blueintegral/Level/firmware/SimpliciTI-CCS-1.1.1/Components/bsp/boards/CC430EM/schematics/EM430F6137RF900.pdf

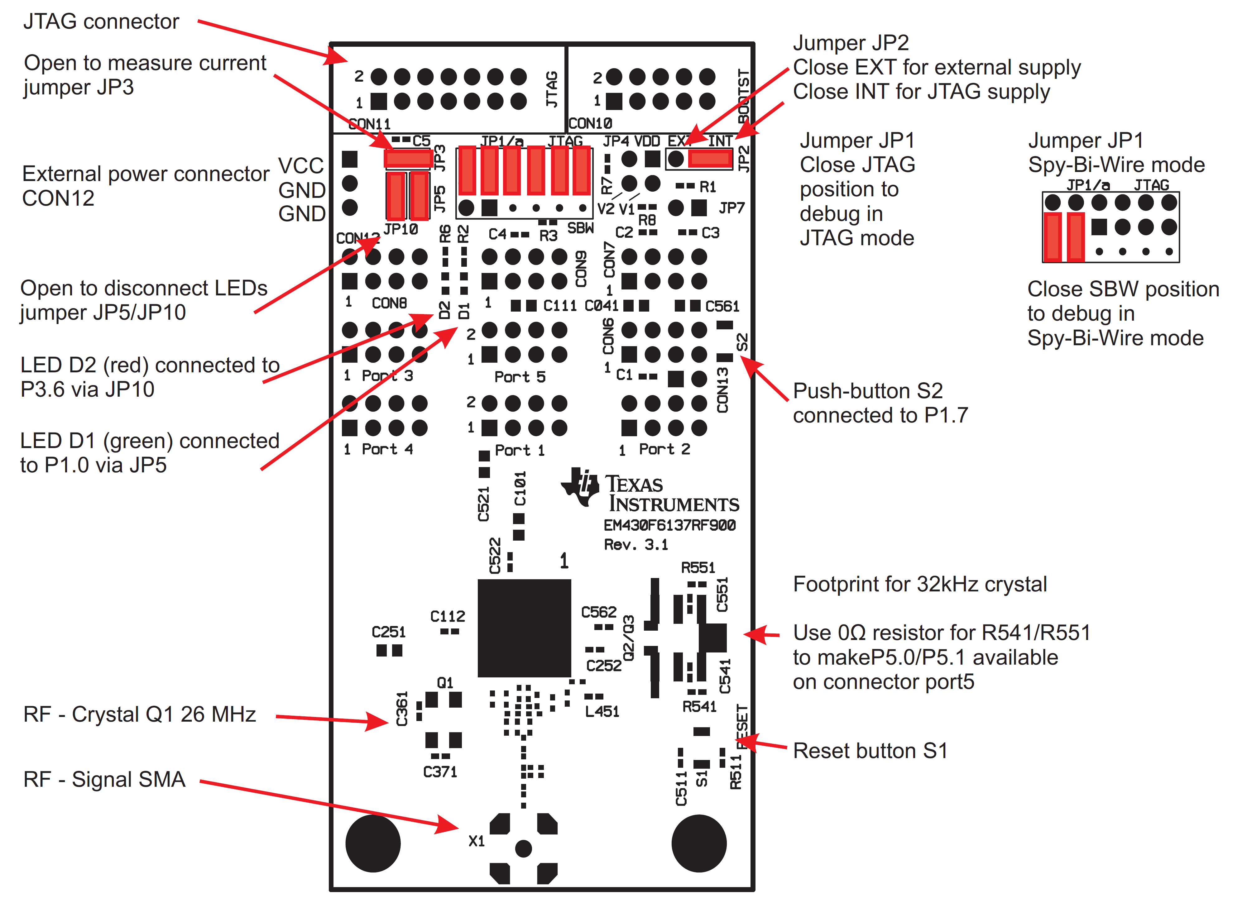
[picture p4: page 1]
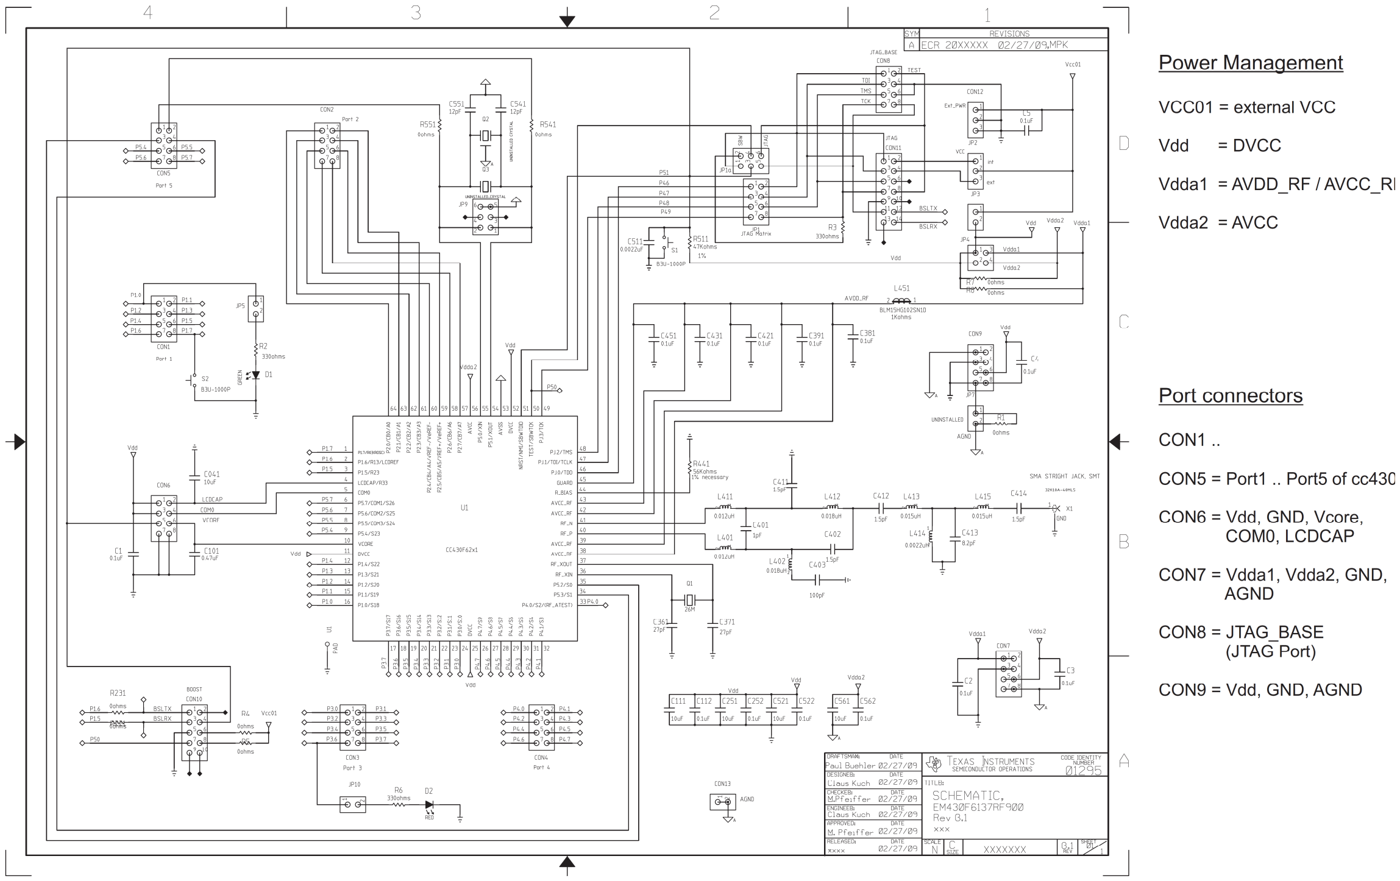
[picture p5: page 2]
