blueintegral/Level/firmware/SimpliciTI-CCS-1.1.1/Components/bsp/boards/EXP461x/schematics/MSP-EXP430FG4618 Schematic.pdf

RF Daughter Card Connect | Isolated RS232 Communication
MSP430FG4618 Pin Access | Power Supply Configuration

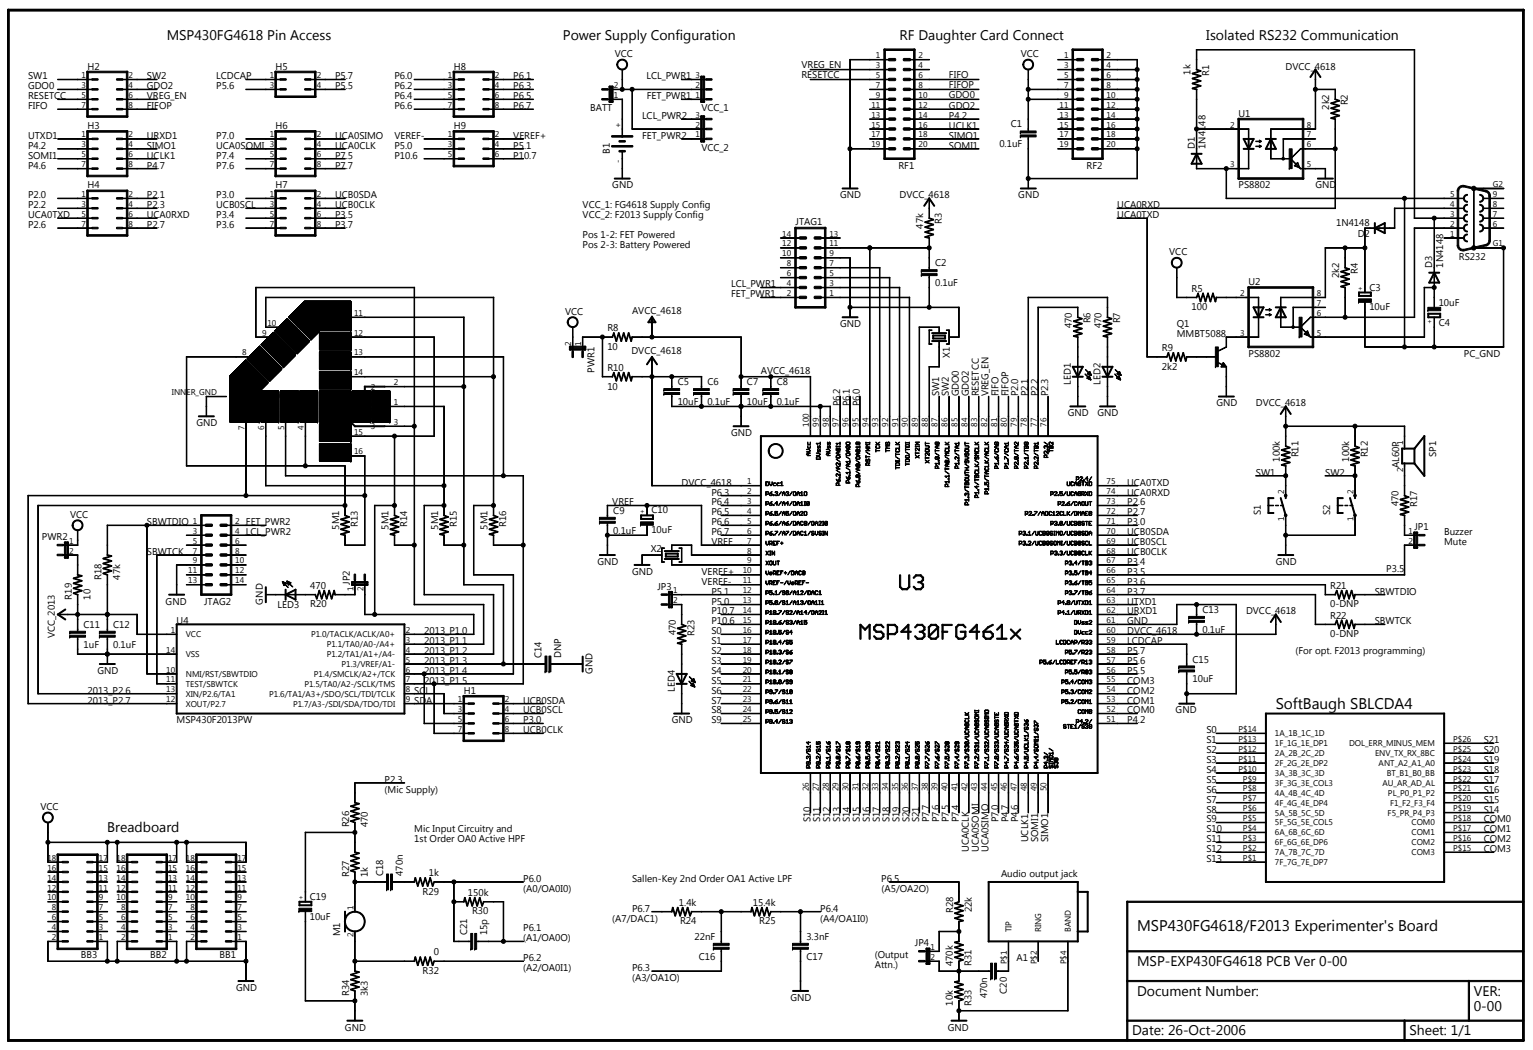
[picture p22: page 1]

P1.6/TA1/A3+/SDO/SCL/TDI/TCLK 8

Mic Input Circuitry and
1st Order OA0 Active HPF

Sallen-Key 2nd Order OA1 Active LPF
