blueintegral/Level/hardware/Tag Connect footprints/Altium/tc2050-b/totc/tc2050example.pdf

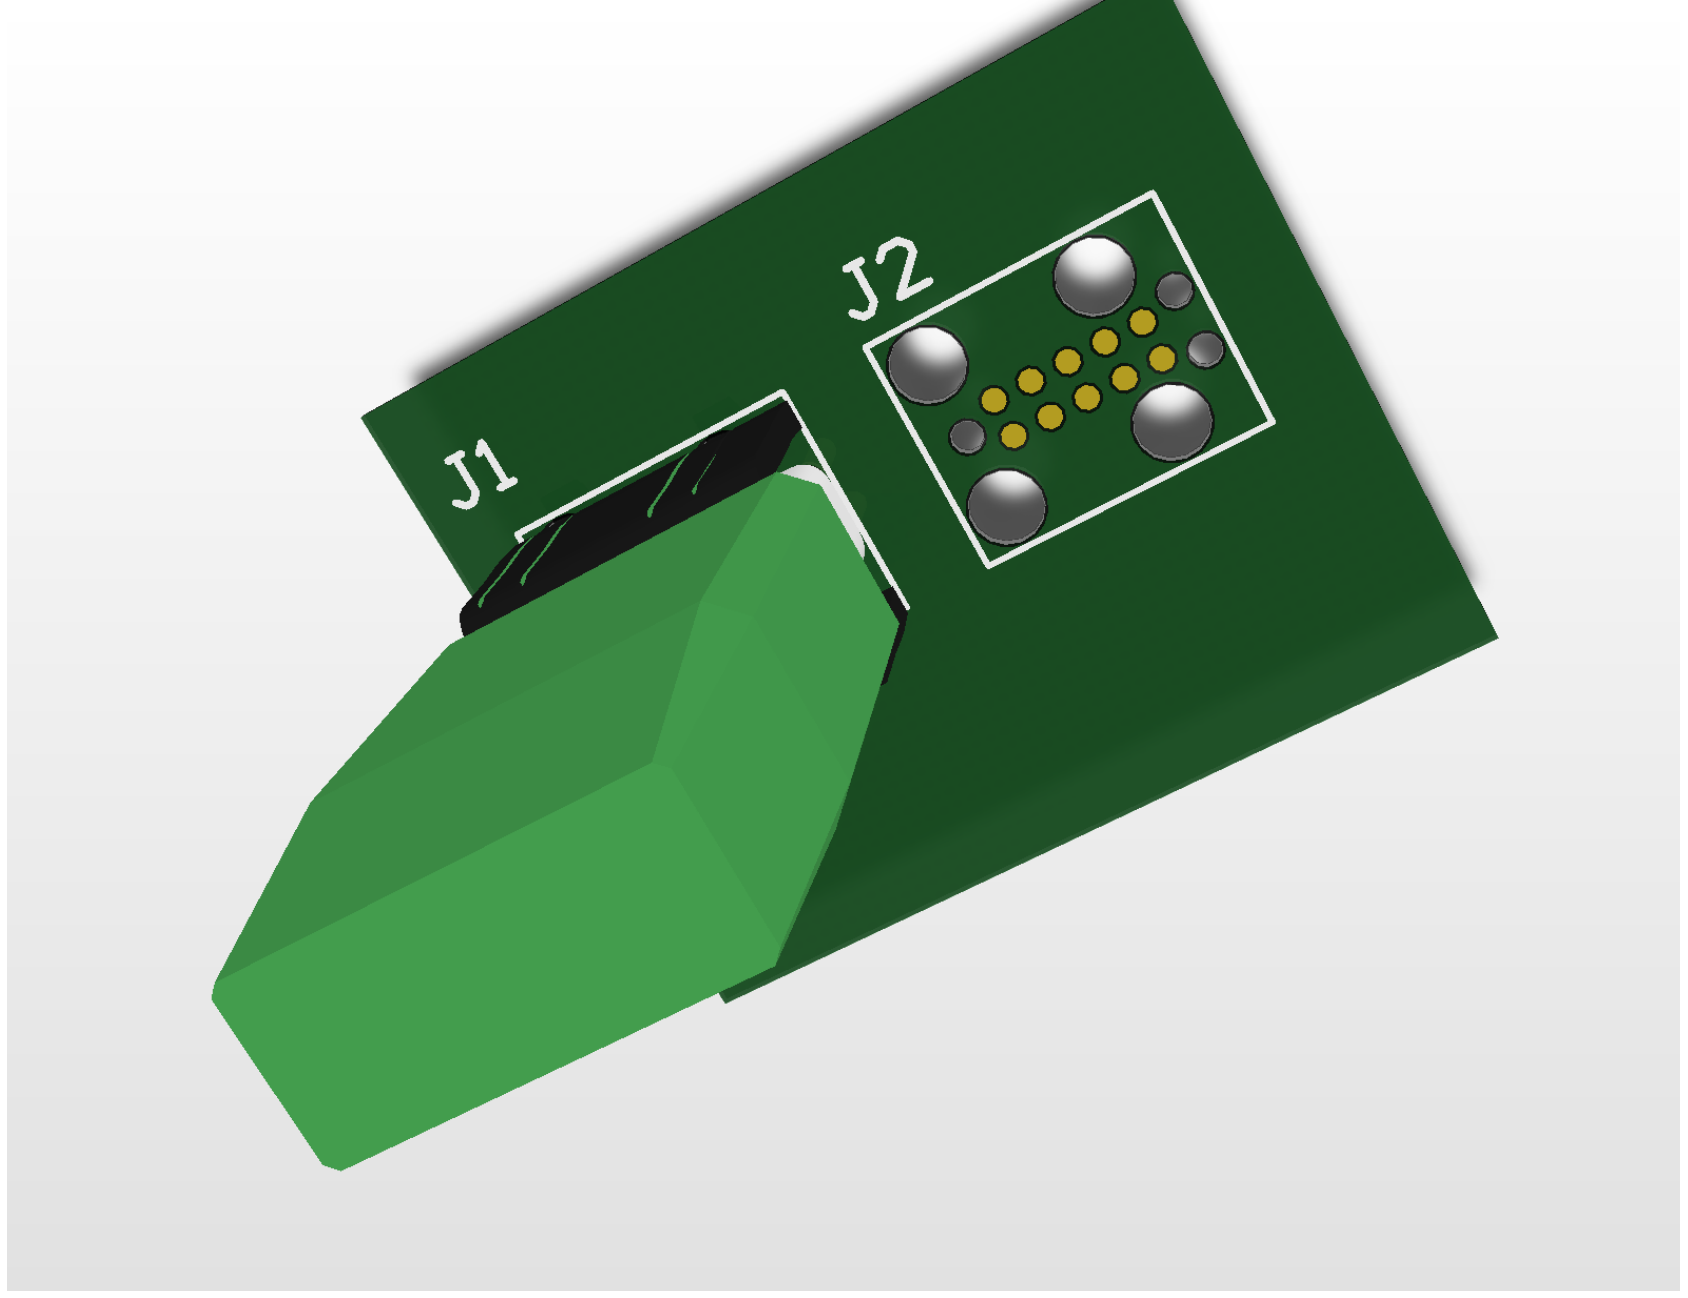
[picture p27: page 1]

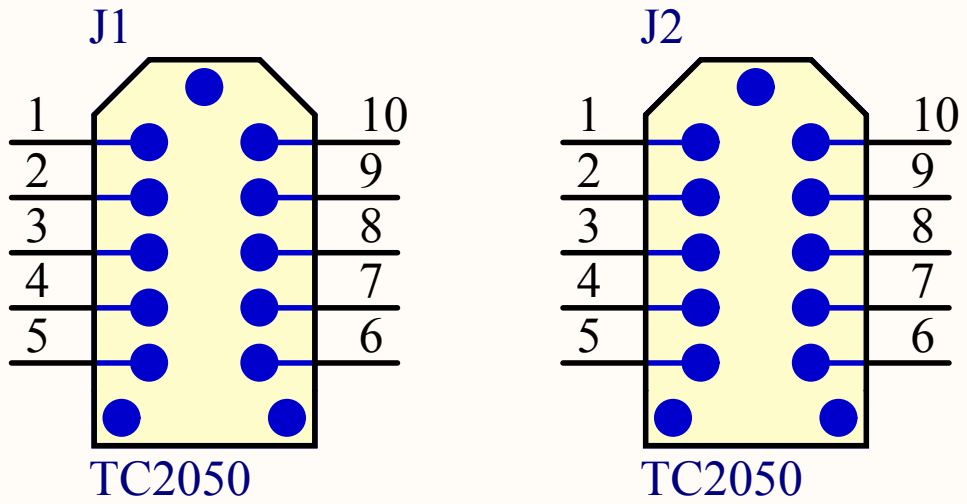
[picture p28: page 2]
