blueintegral/Level/firmware/SimpliciTI-CCS-1.1.1/Components/bsp/boards/EXP461x/schematics/CC1100EM_schematic.pdf

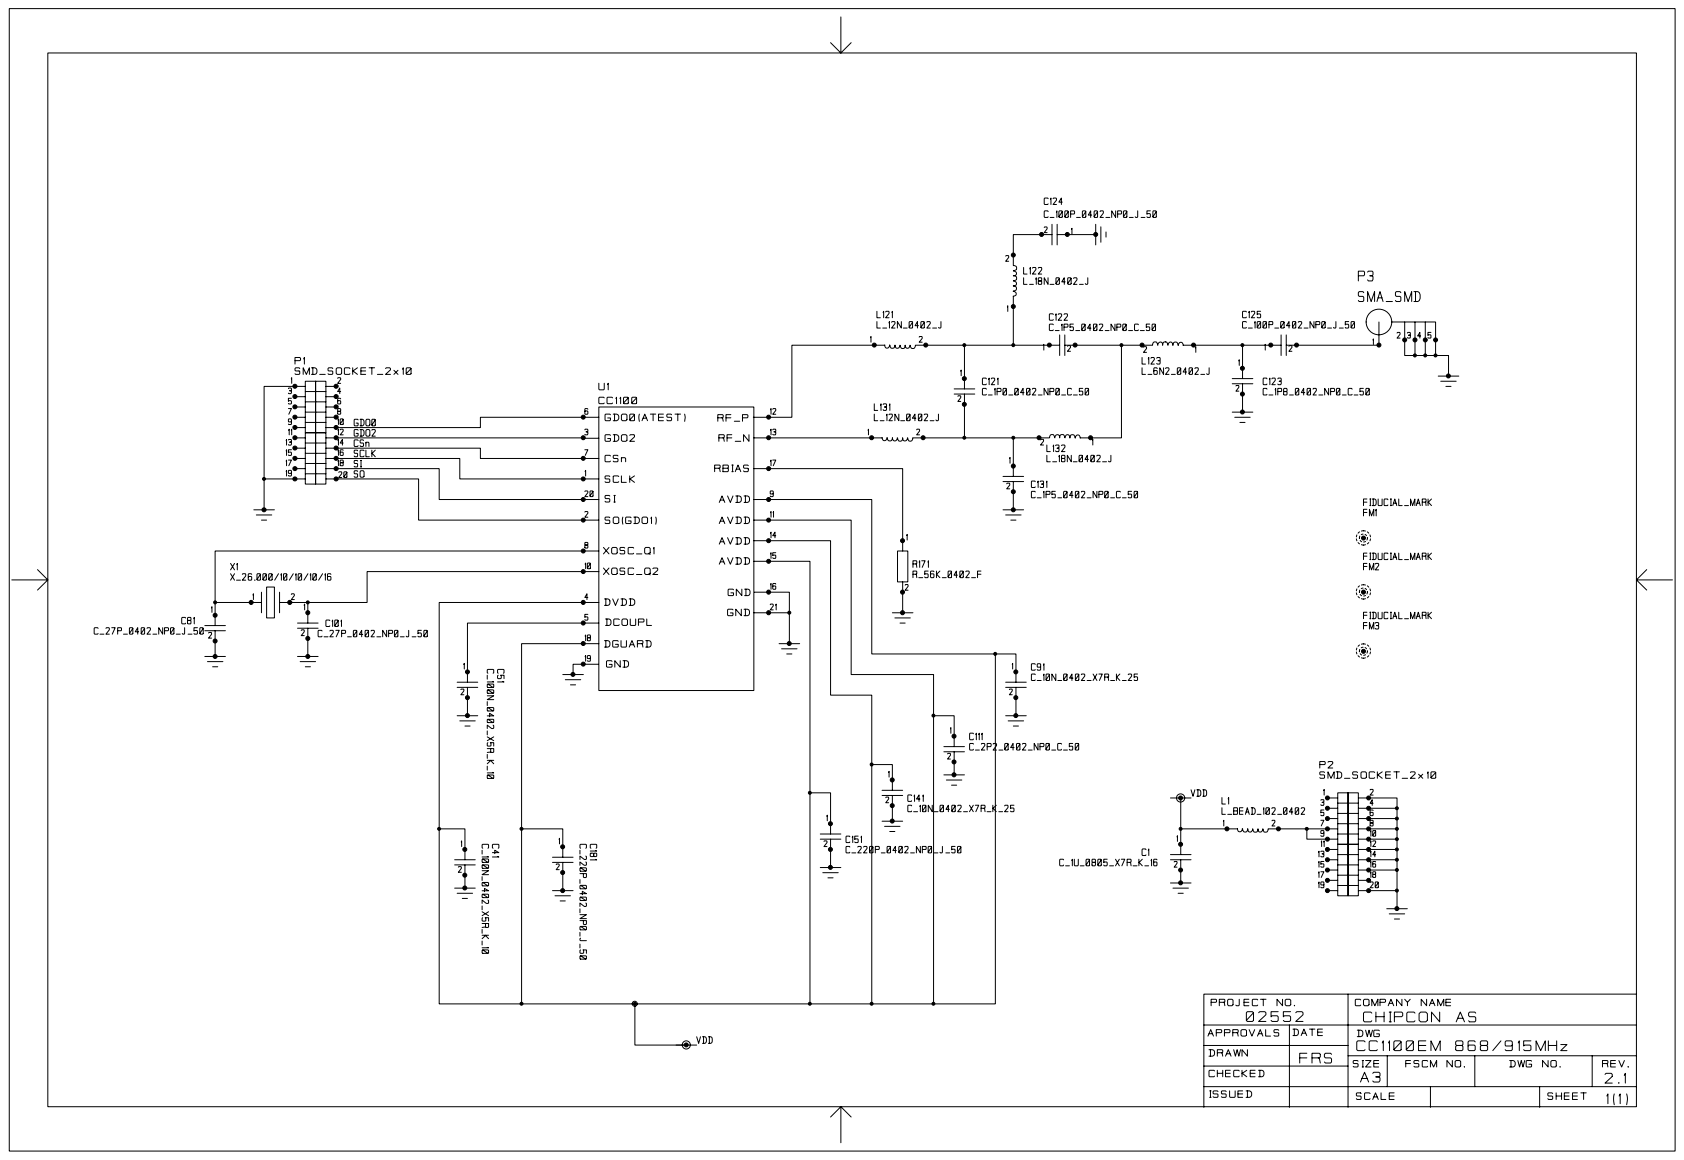
[picture p29: page 1]
