blueintegral/Level/firmware/SimpliciTI-CCS-1.1.1/Components/bsp/boards/EXP461x/schematics/CC2500EM_schematic.pdf

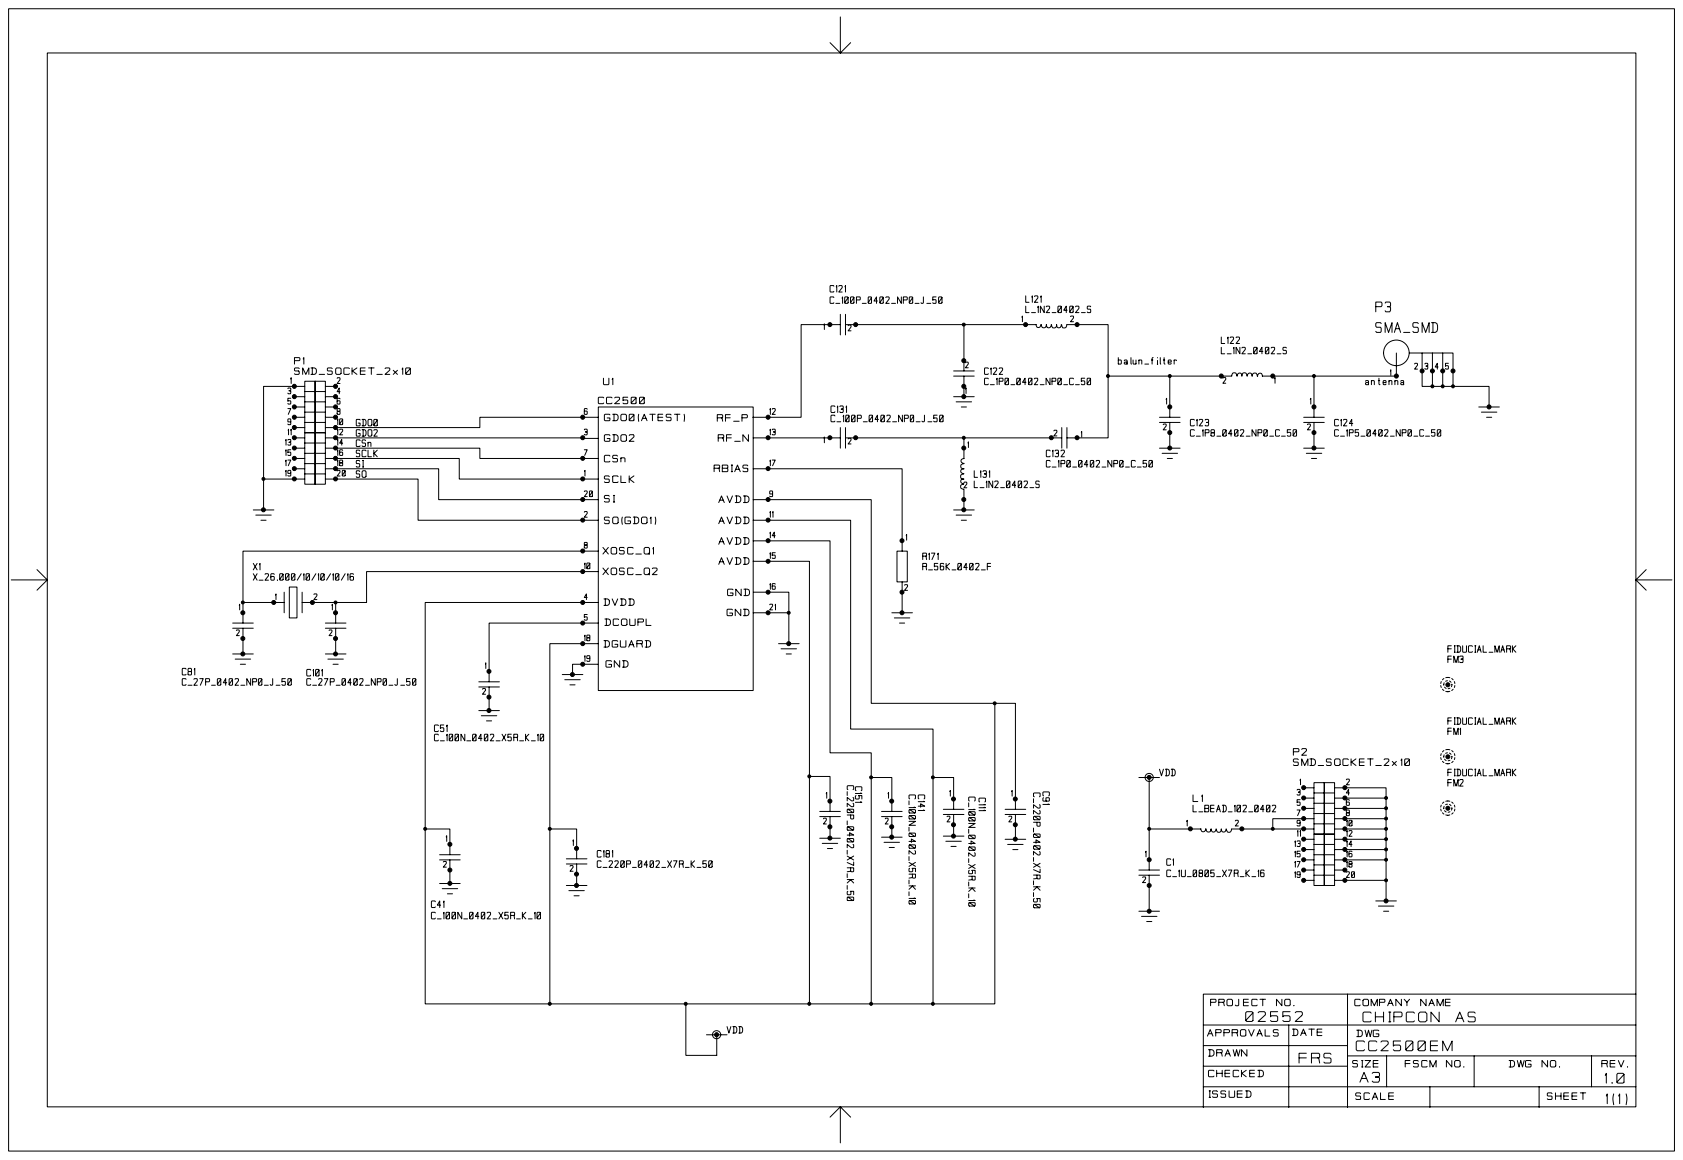
[picture p30: page 1]
