blueintegral/Level/firmware/SimpliciTI-CCS-1.1.1/Components/bsp/boards/EZ430RF/schematics/AMB2521_HW-V1.0_20070403_sch.pdf

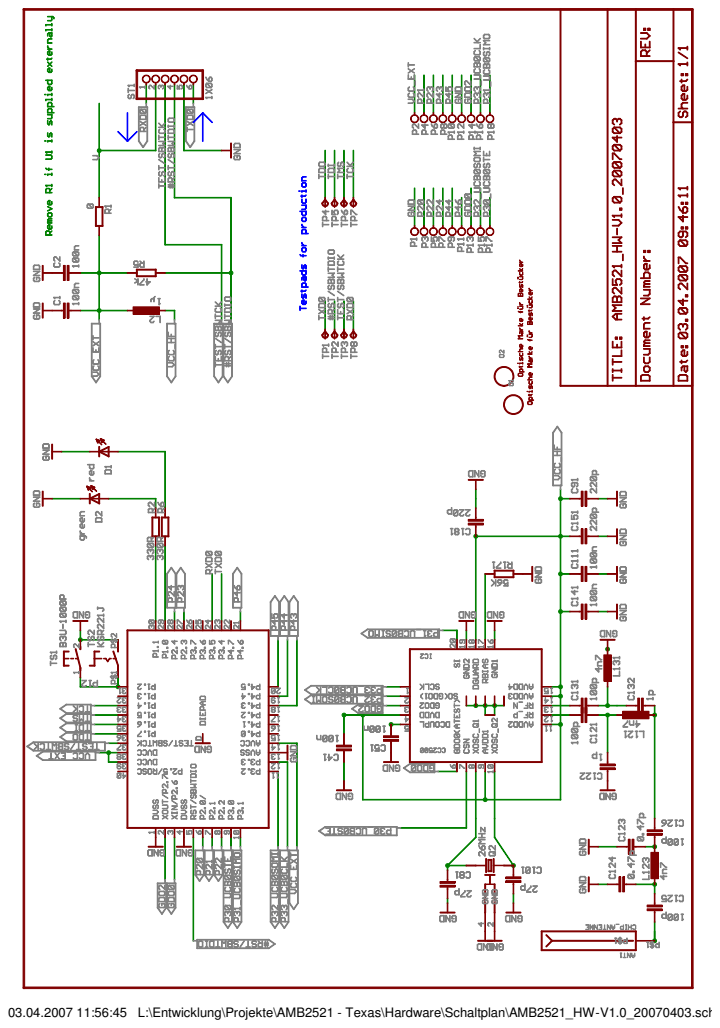
[picture p31: page 1]

03.04.2007 11:56:45 L:\Entwicklung\Projekte\AMB2521 - Texas\Hardware\Schaltplan\AMB2521_HW-V1.0_20070403.sch
