blueintegral/Level/firmware/SimpliciTI-CCS-1.1.1/Components/bsp/boards/EZ430RF/schematics/eZ430-RF2500_emulator_schematic.pdf

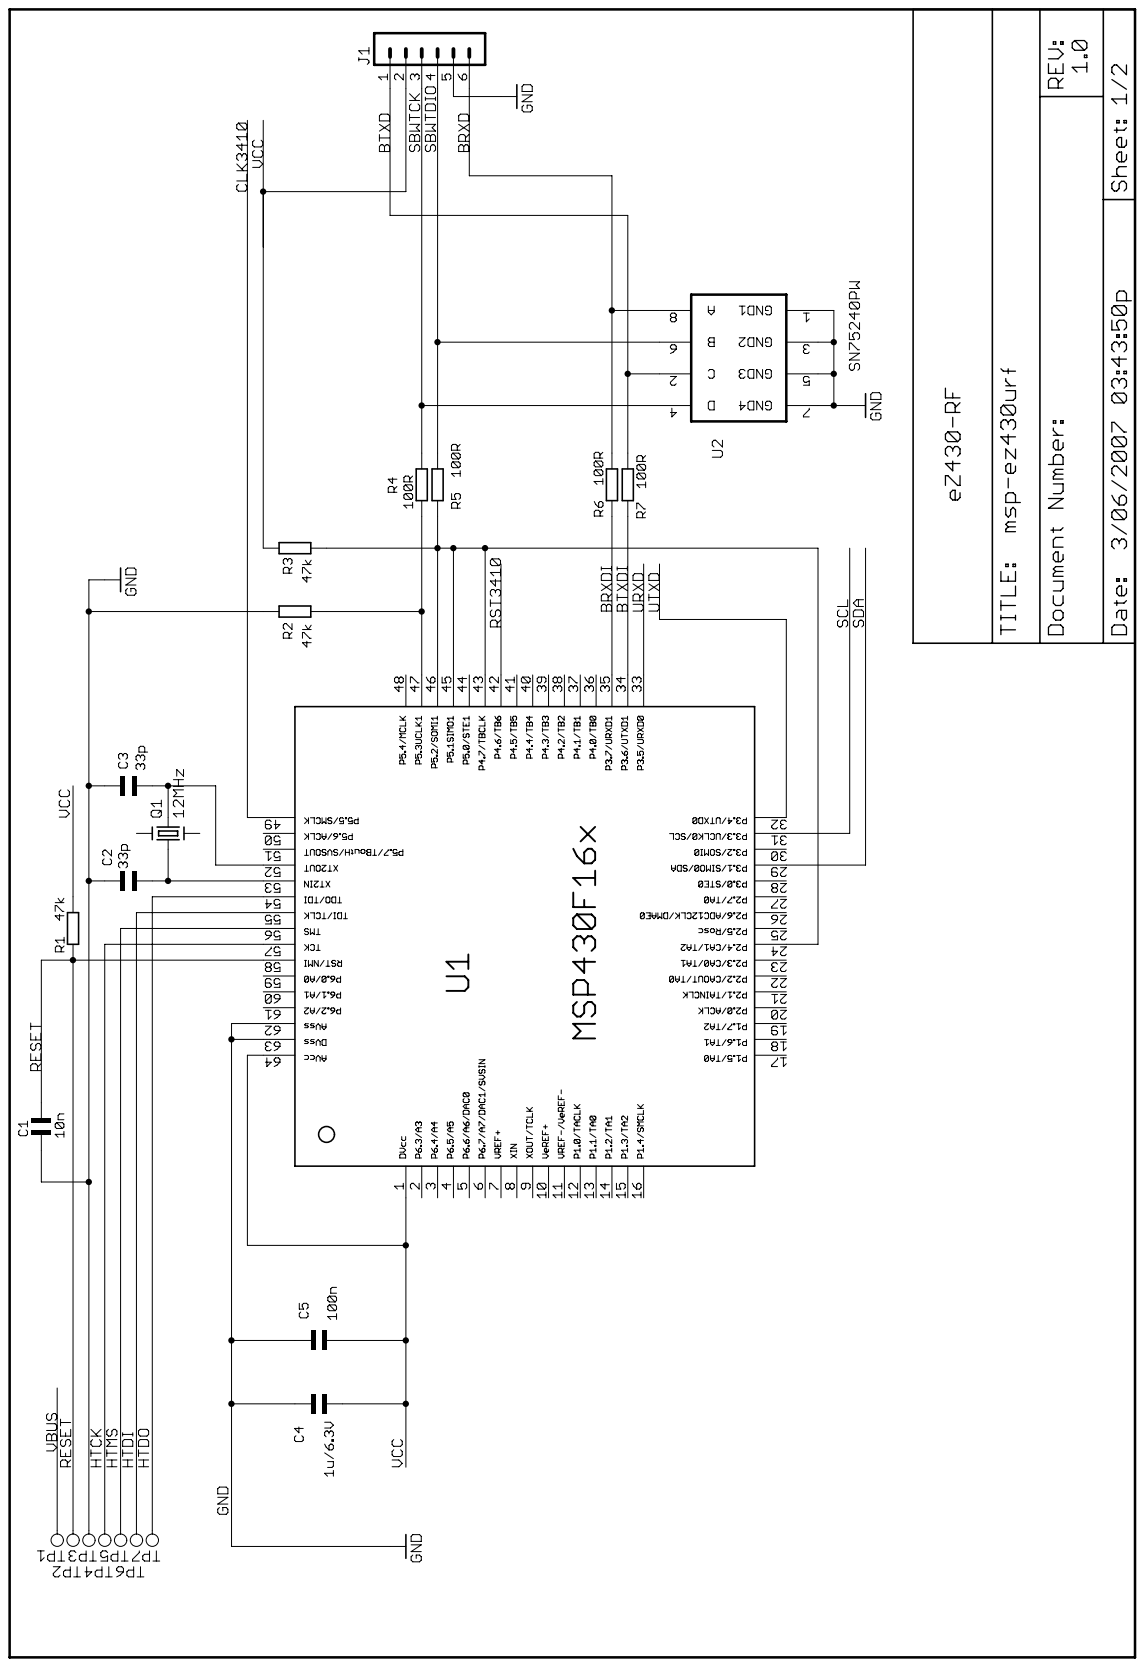
[picture p32: page 1]

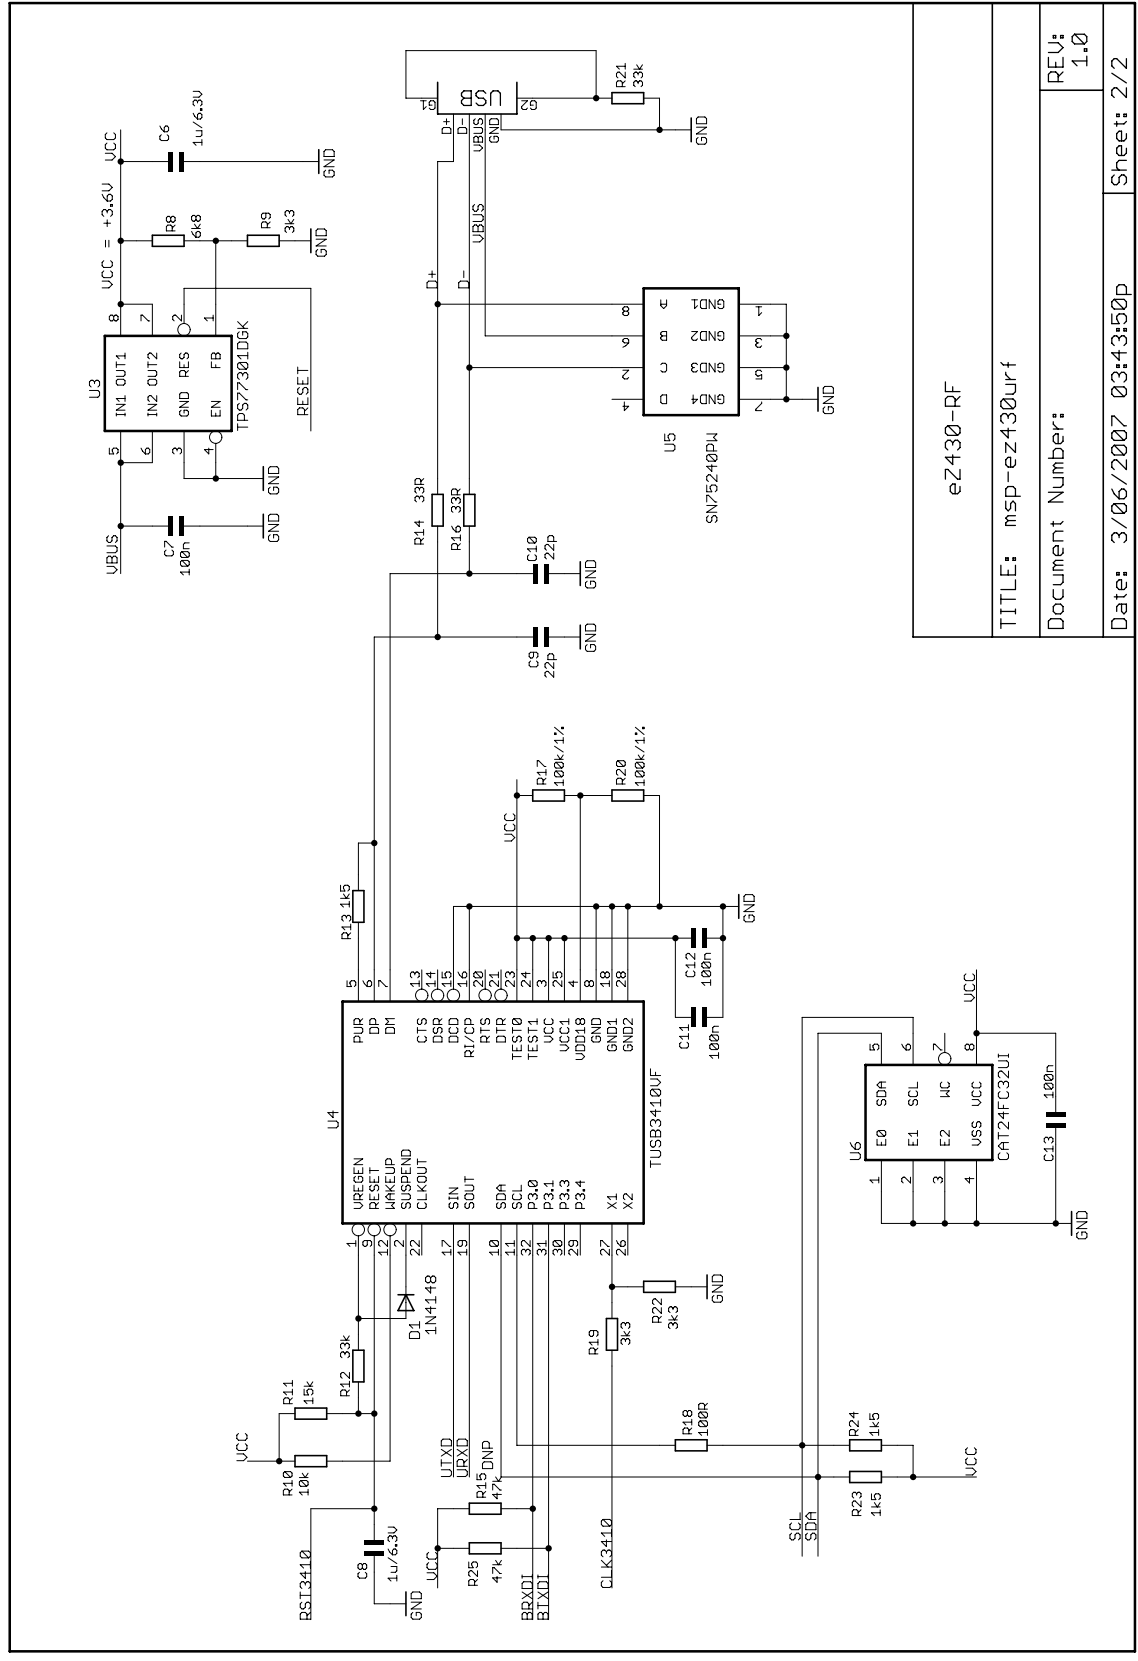
[picture p33: page 2]

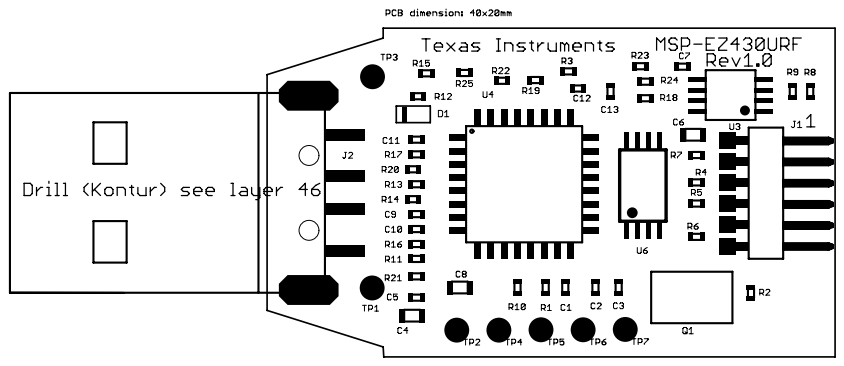
[picture p34: page 3]

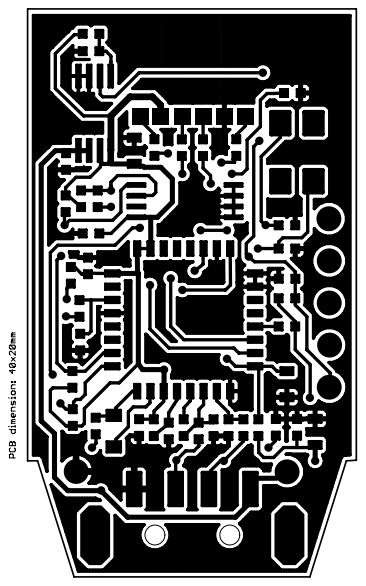
[picture p35: page 4]

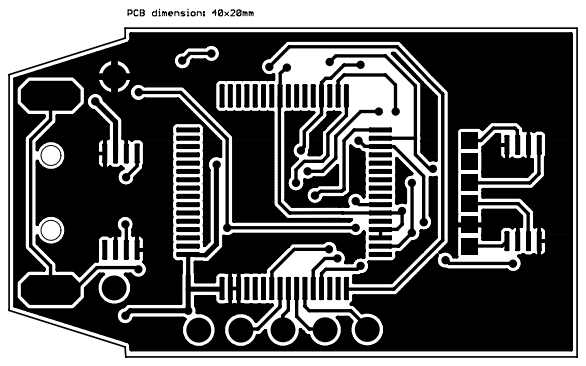
[picture p36: page 5]
