blueintegral/Level/firmware/SimpliciTI-CCS-1.1.1/Components/bsp/boards/SRF05EB/schematics/CC2520EM_2_1_Schematic.pdf

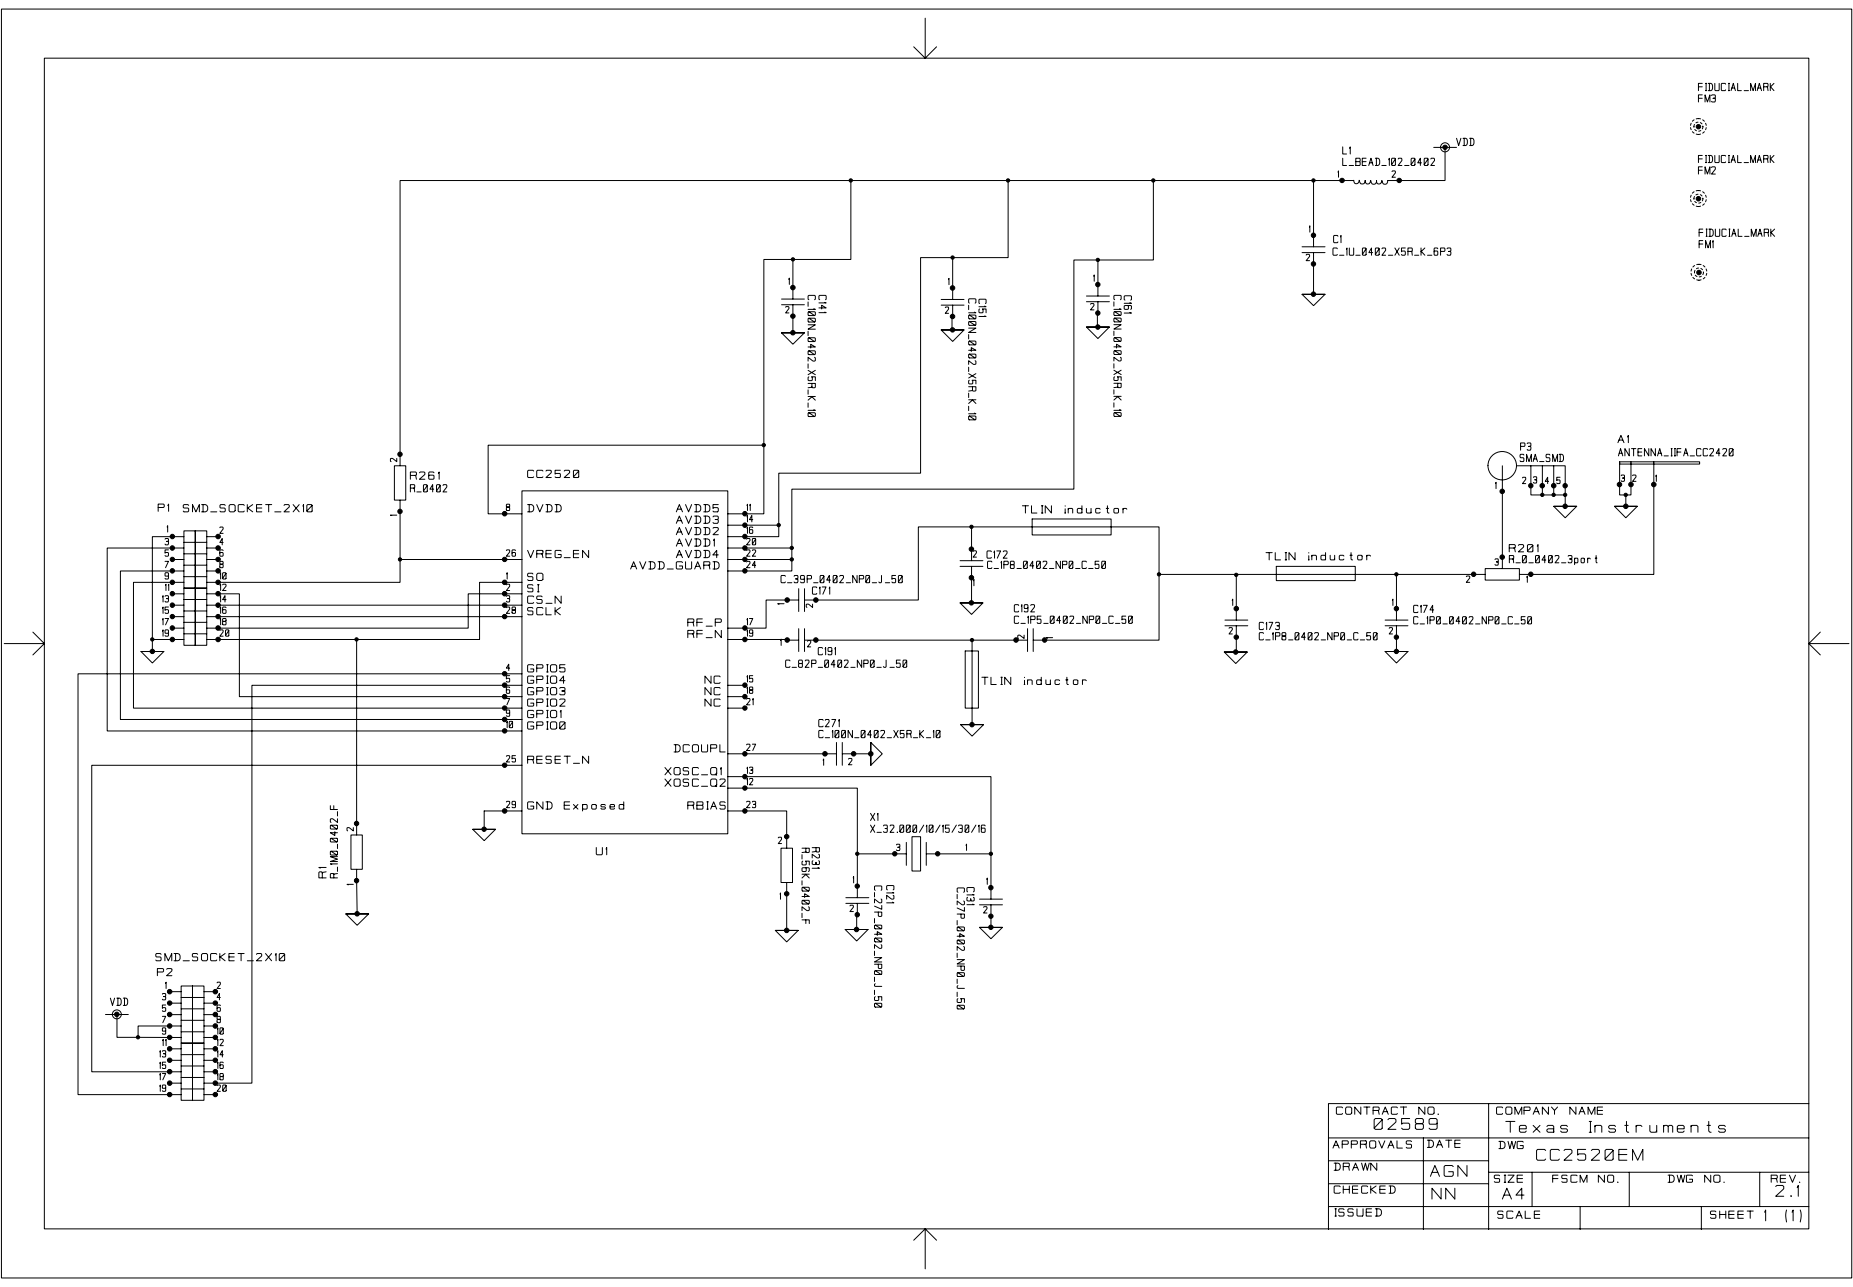
[picture p37: page 1]
