blueintegral/Level/firmware/SimpliciTI-CCS-1.1.1/Components/bsp/boards/SRF05EB/schematics/CCMSP-EM430F2618_1_0.pdf

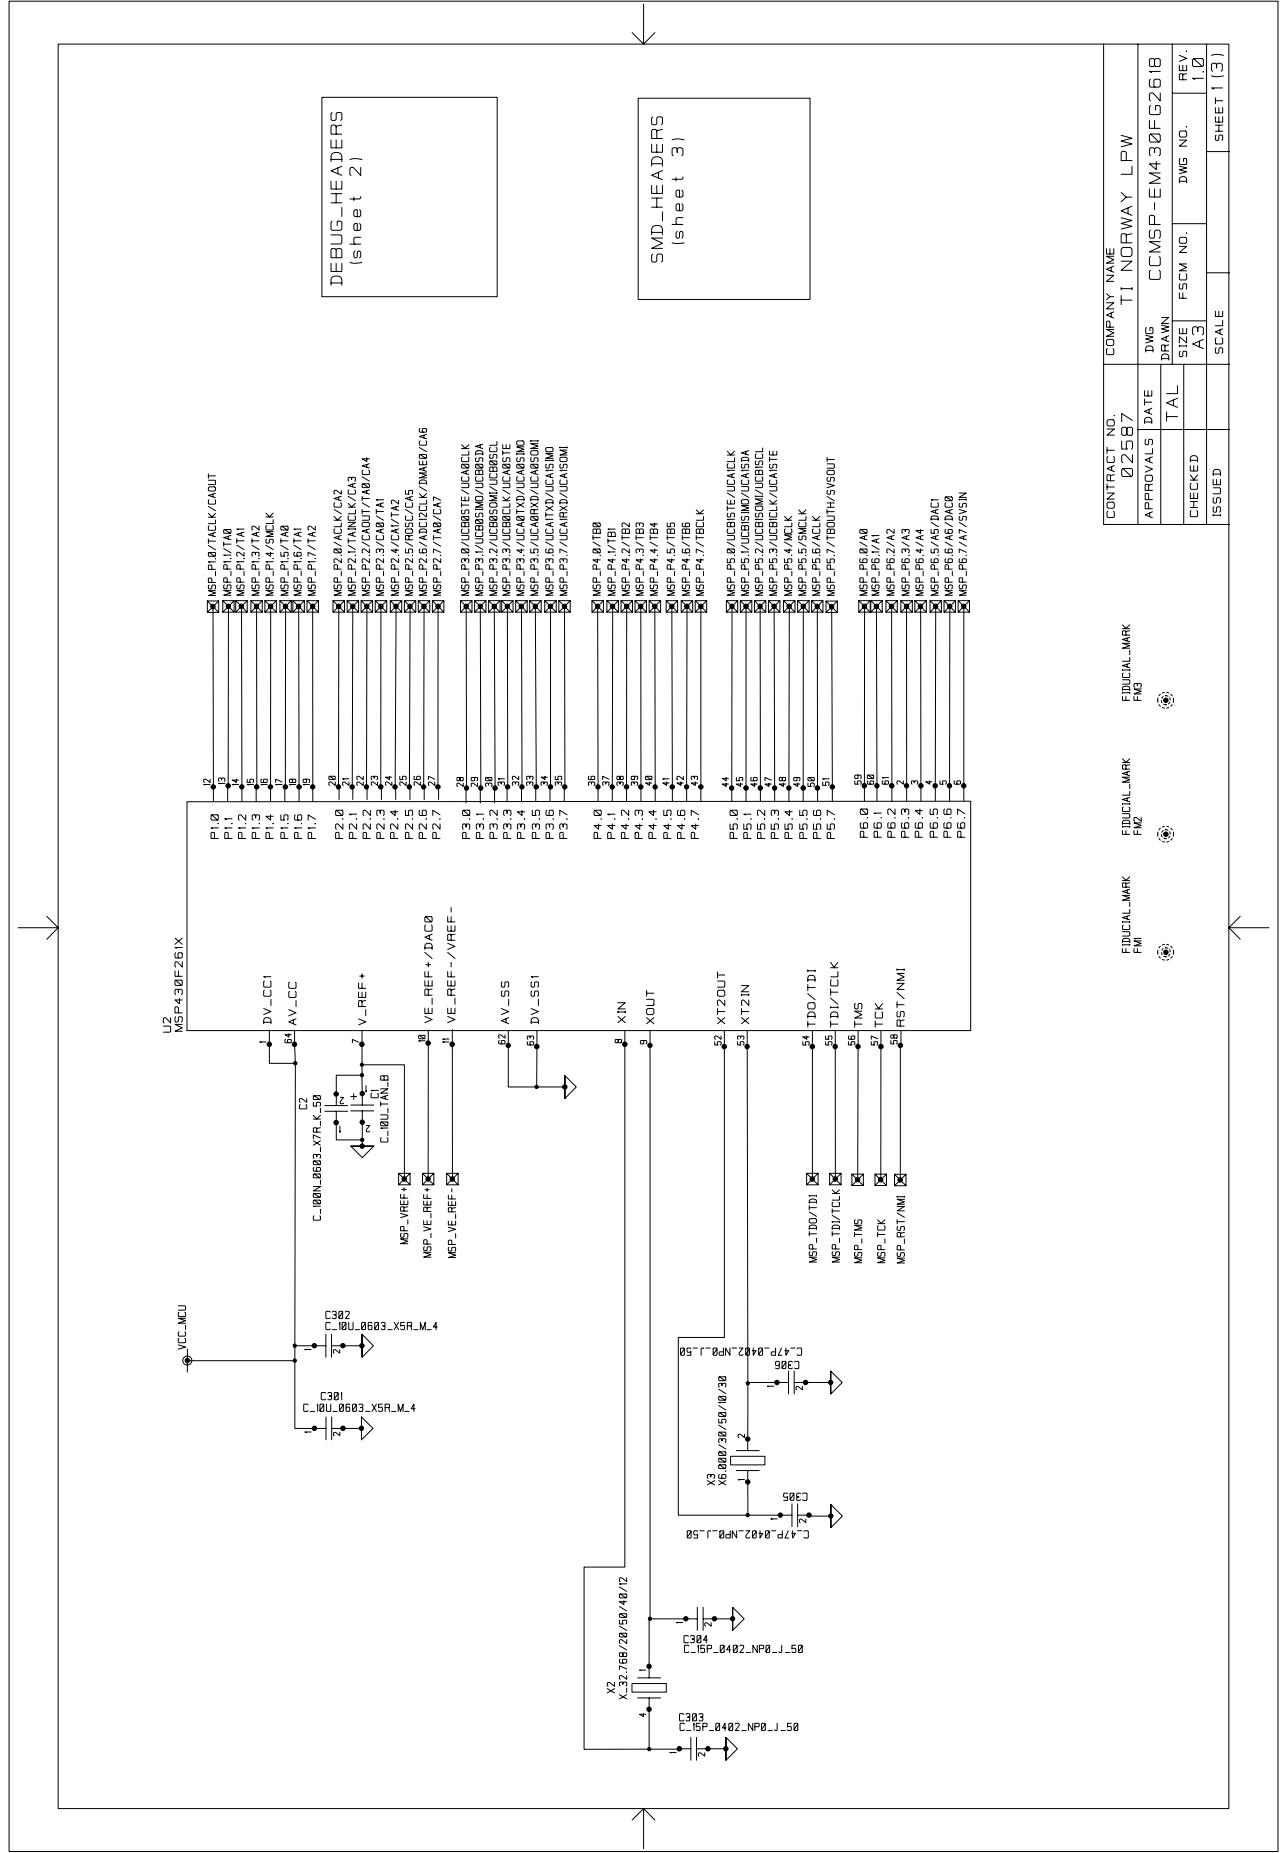
[picture p38: page 1]

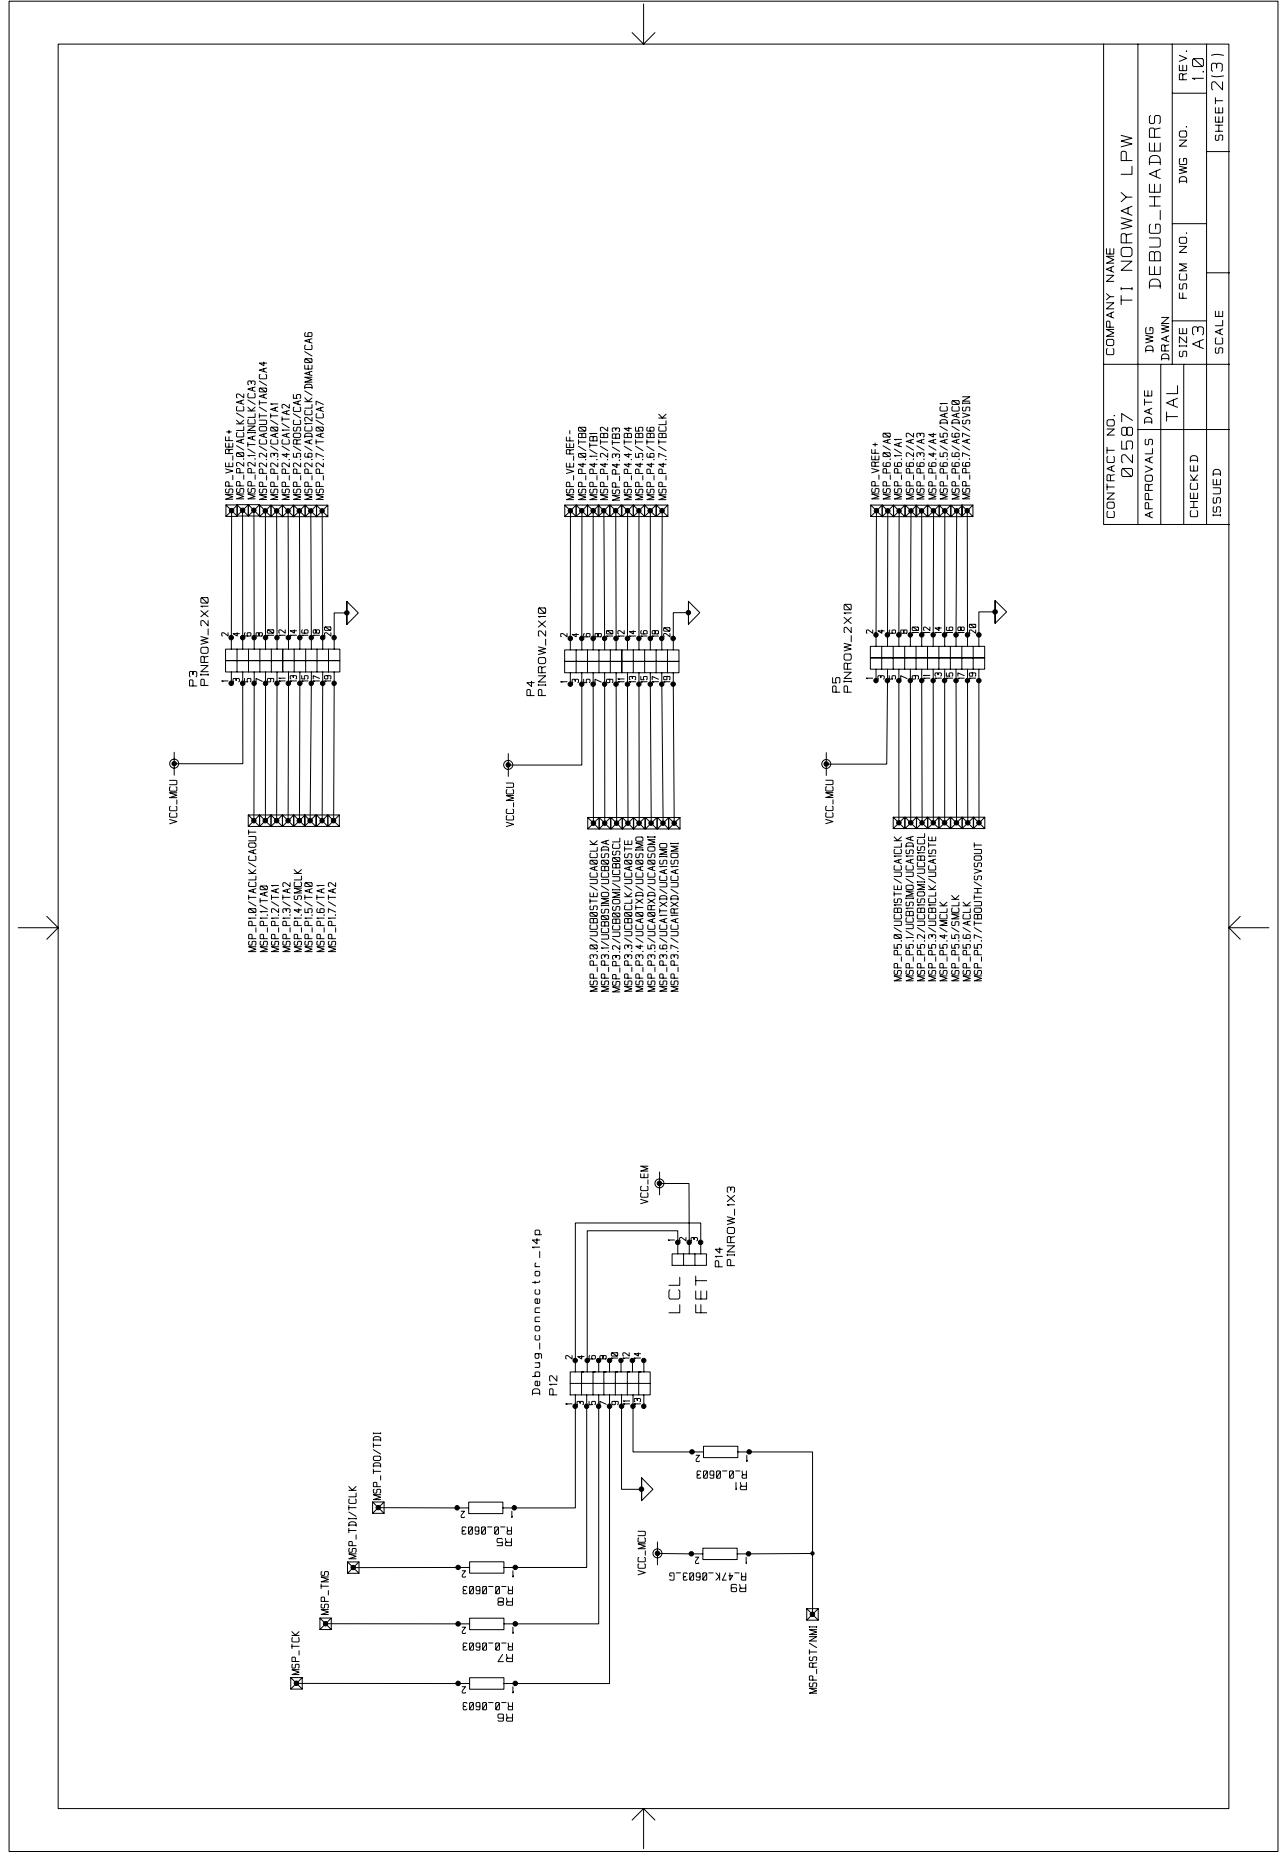
[picture p39: page 2]

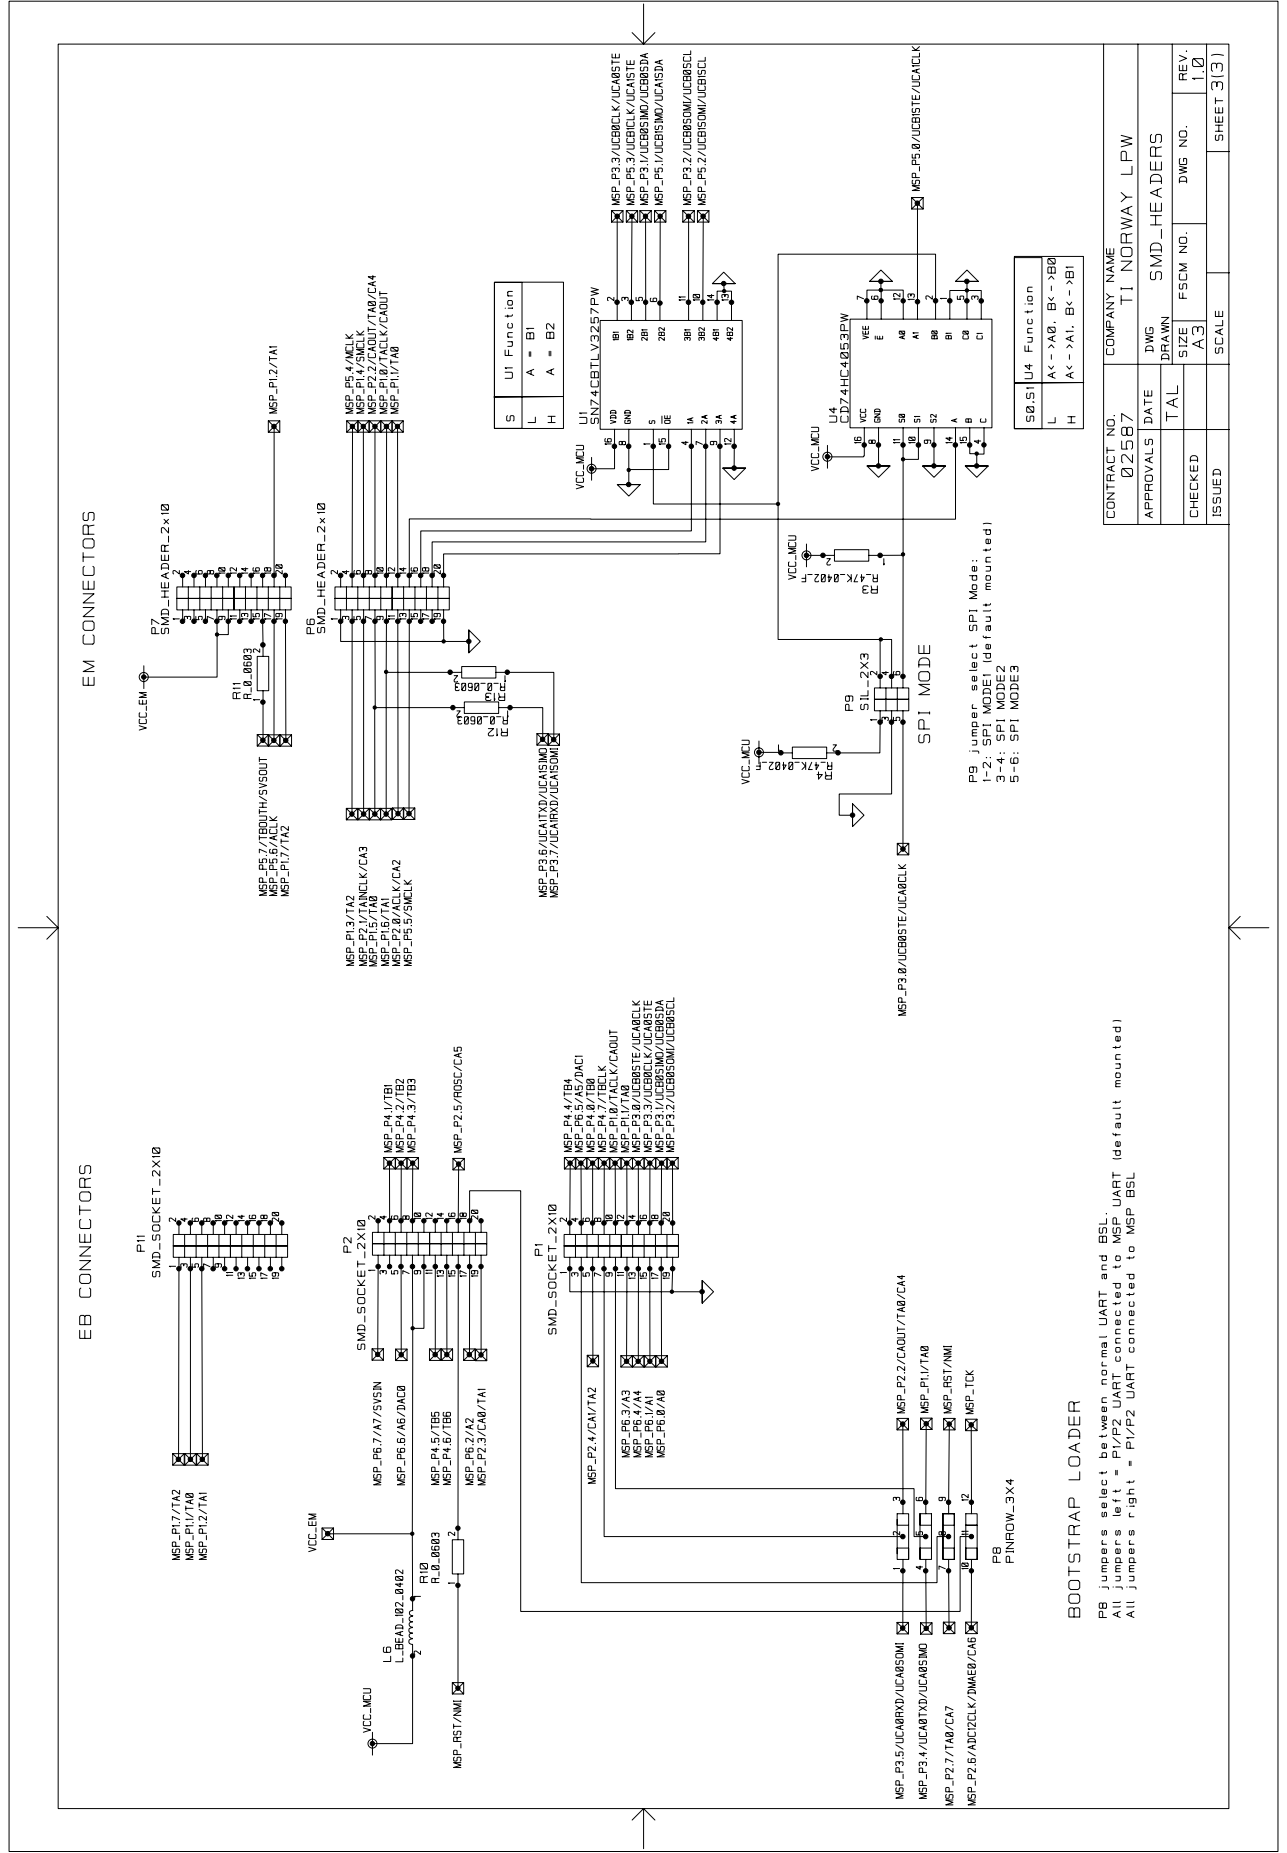
[picture p40: page 3]
