blueintegral/Level/firmware/SimpliciTI-CCS-1.1.1/Components/bsp/boards/SRF05EB/schematics/SmartRF05EB_1_2.pdf

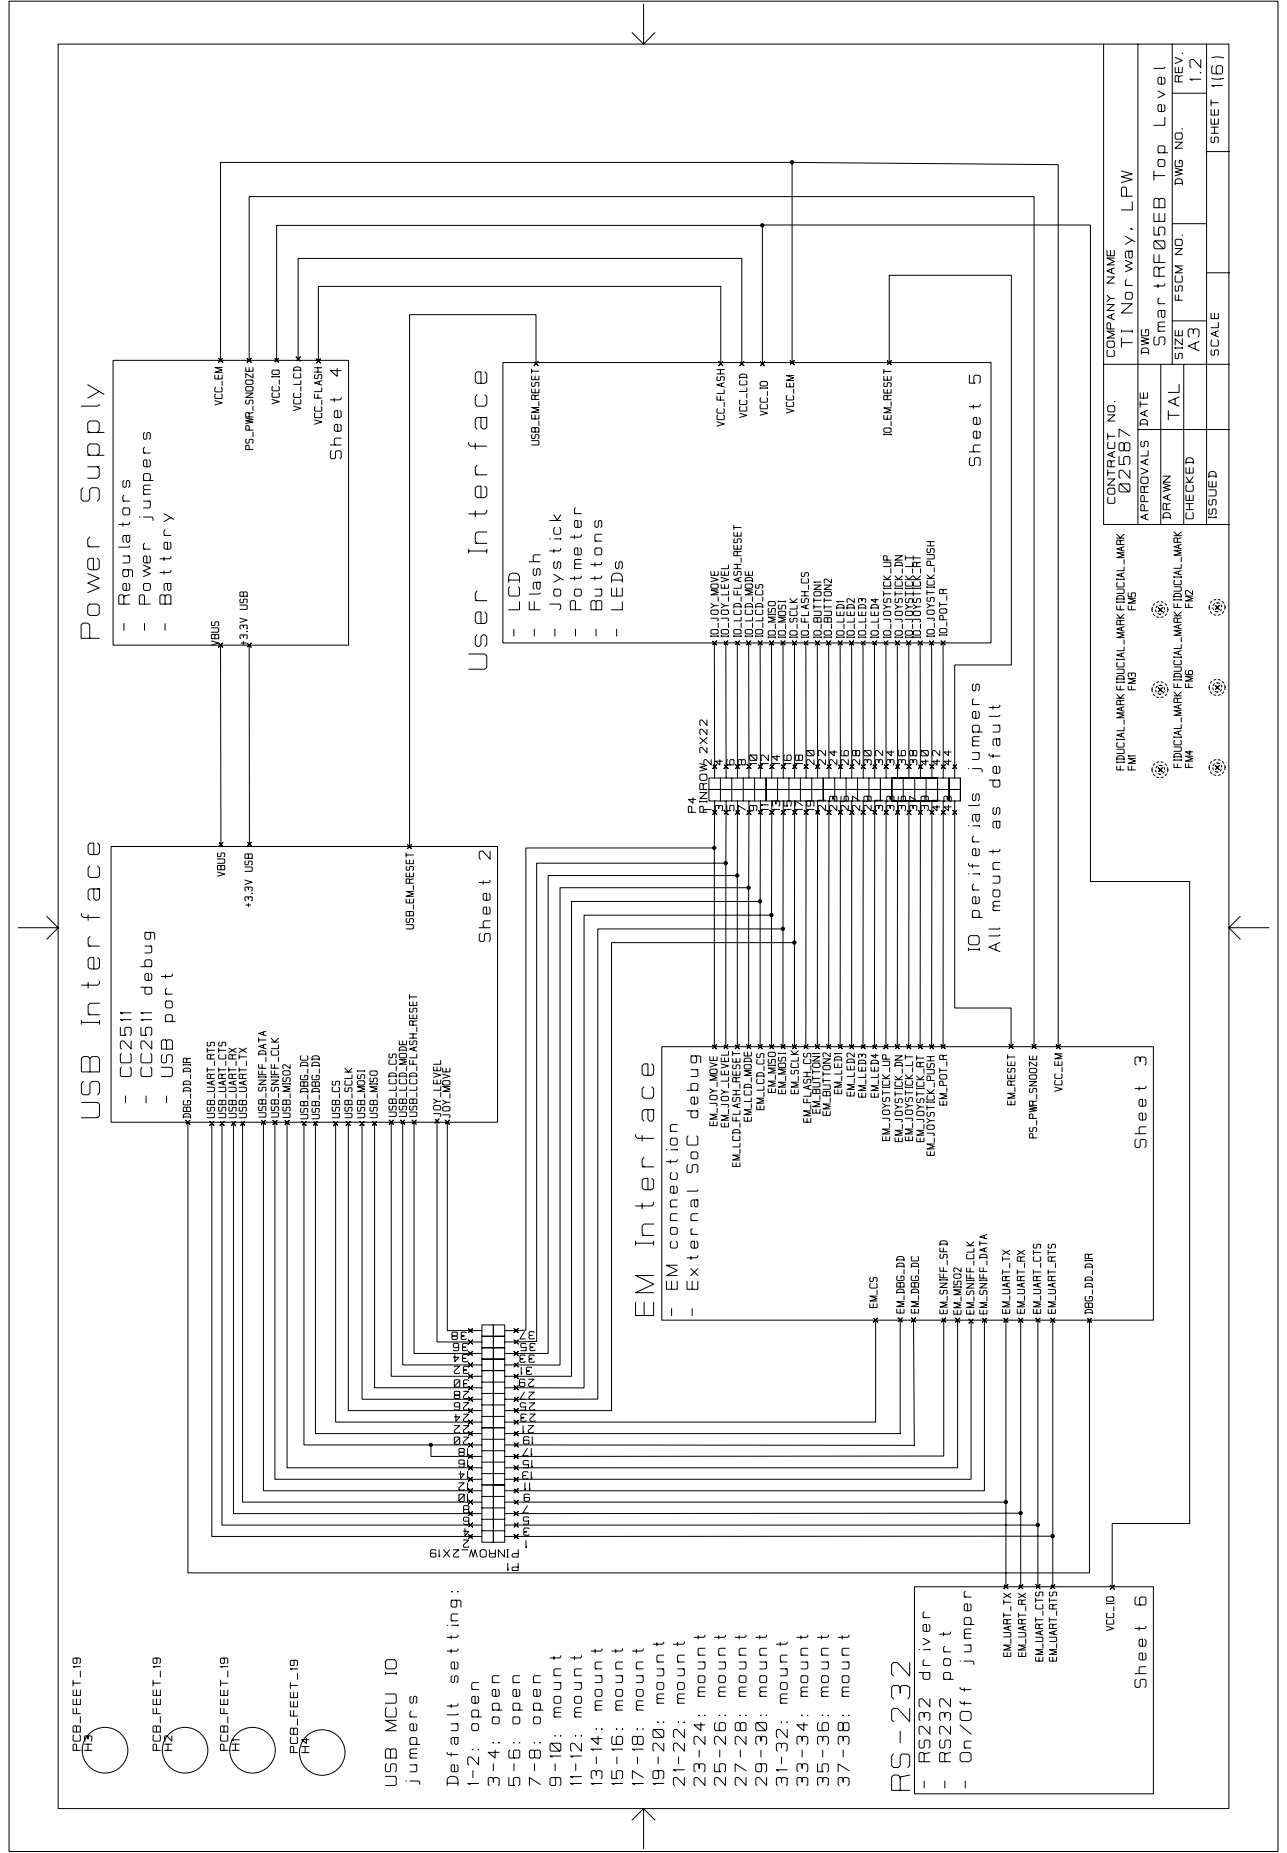
[picture p41: page 1]

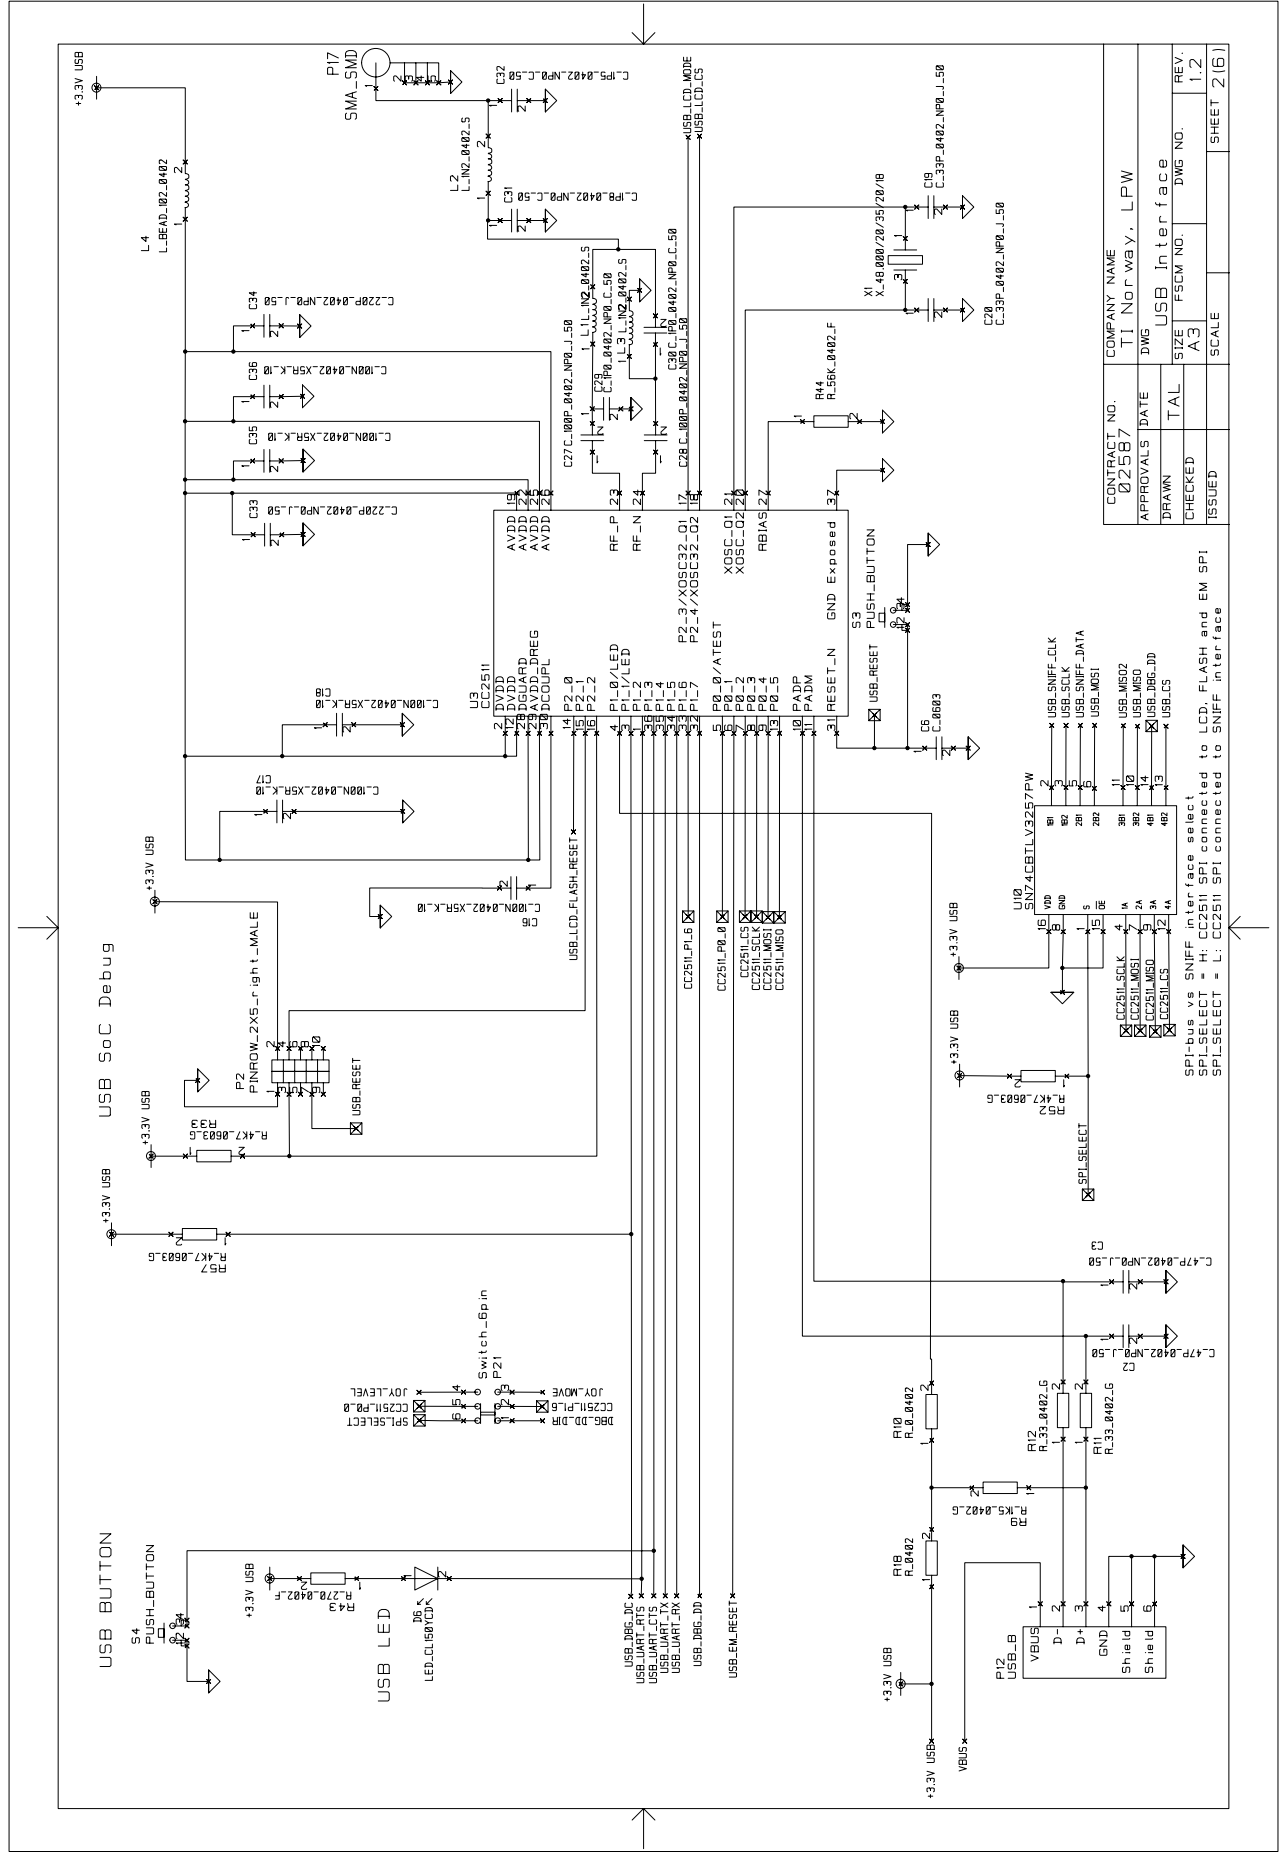
[picture p42: page 2]

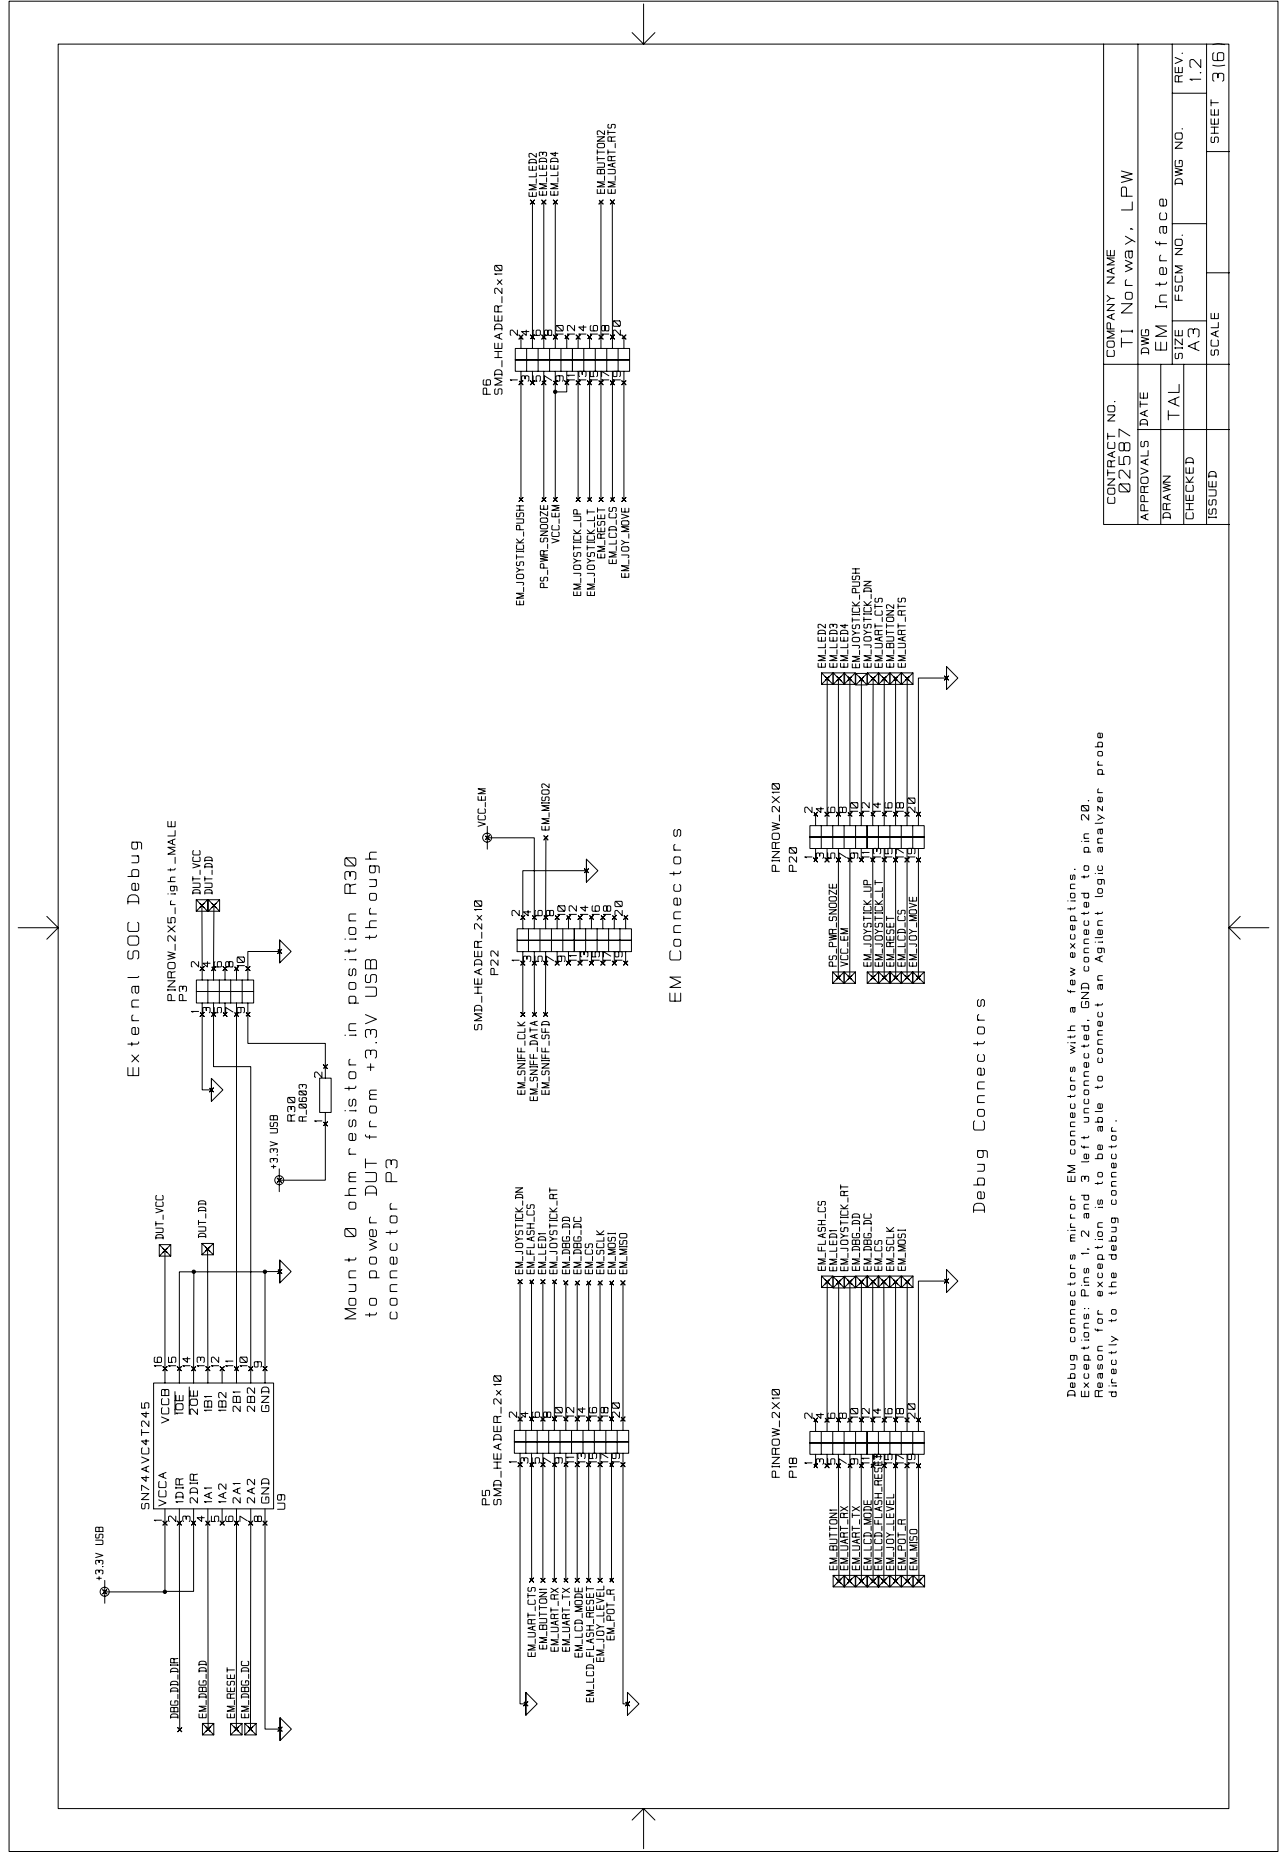
[picture p43: page 3]

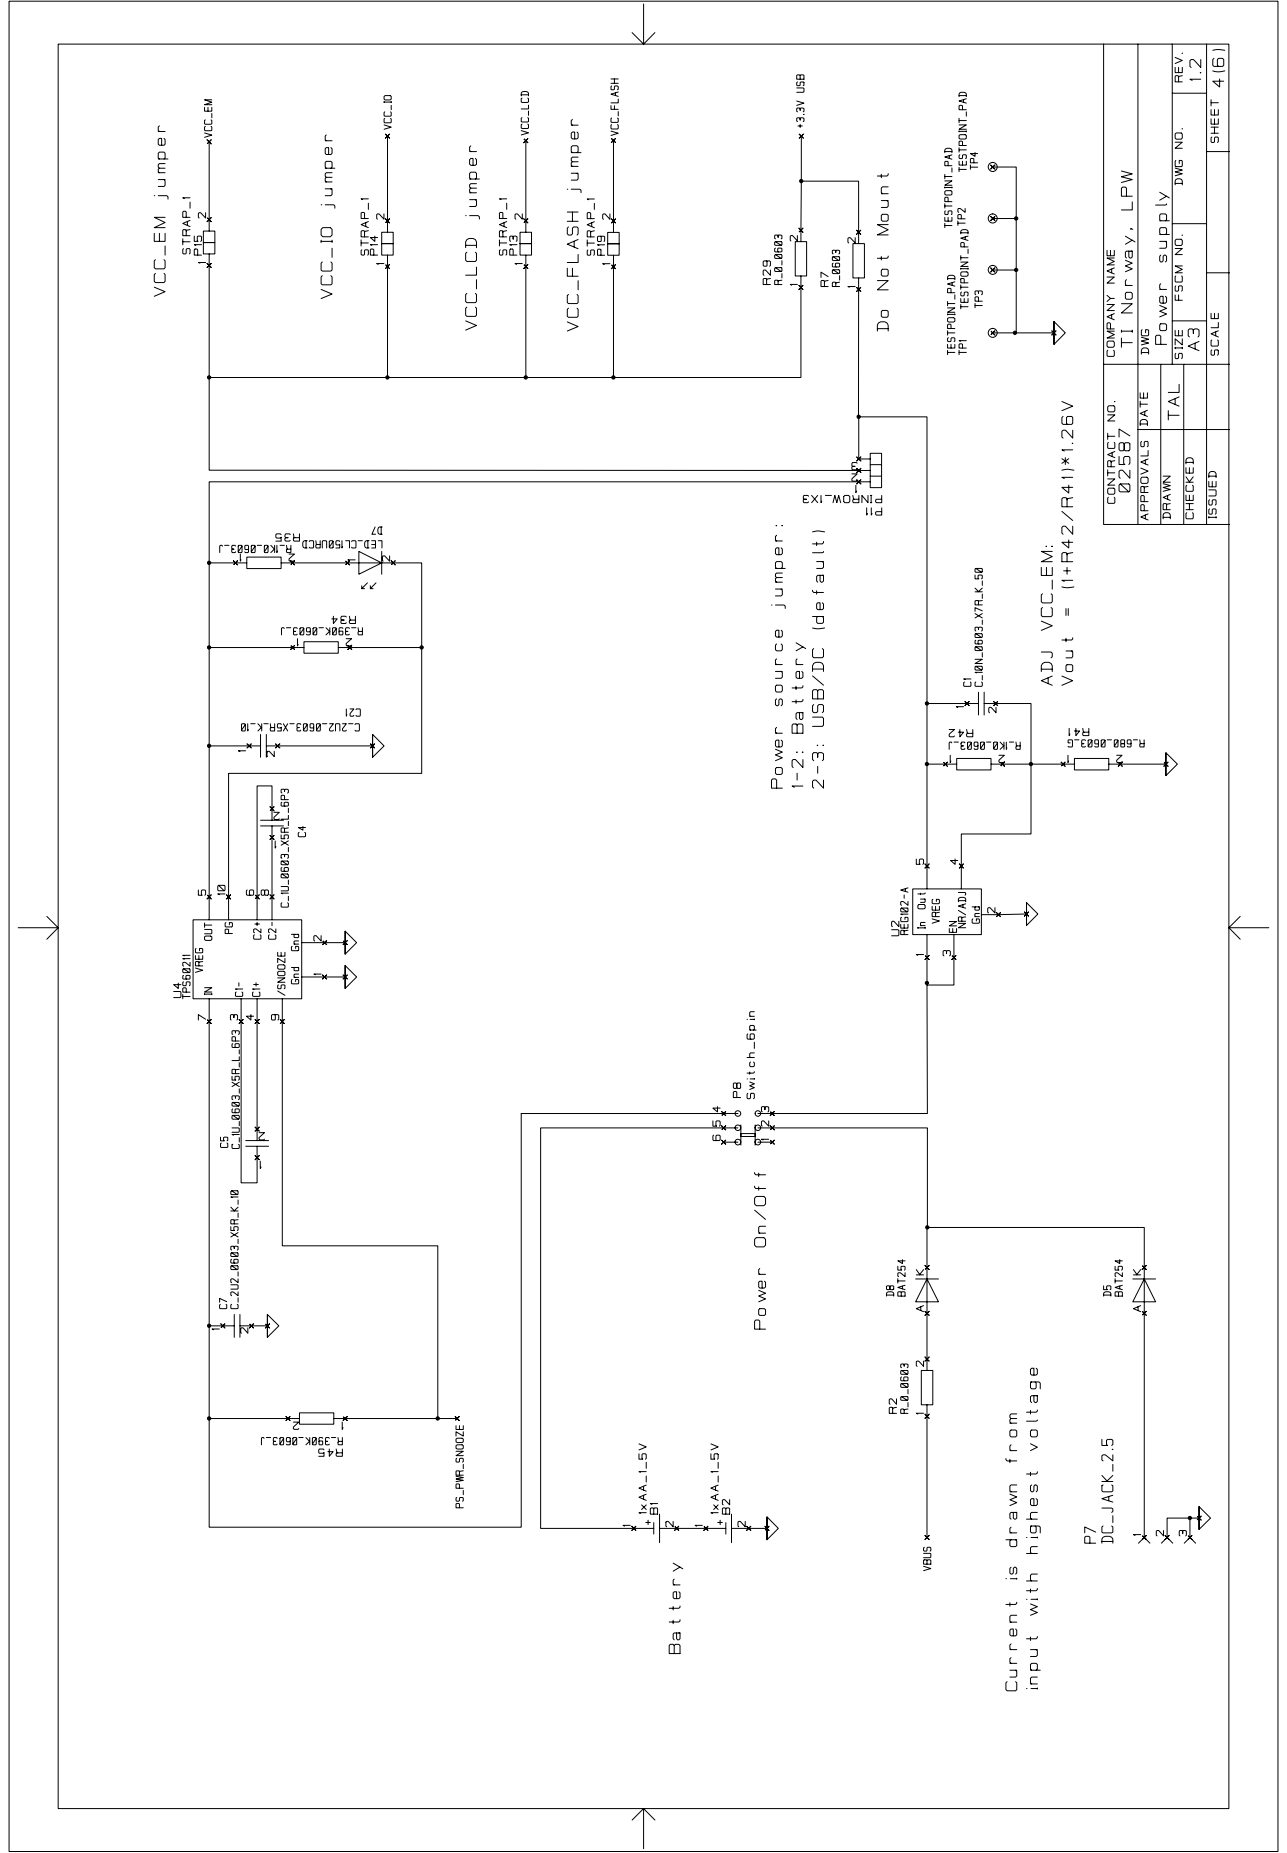
[picture p44: page 4]

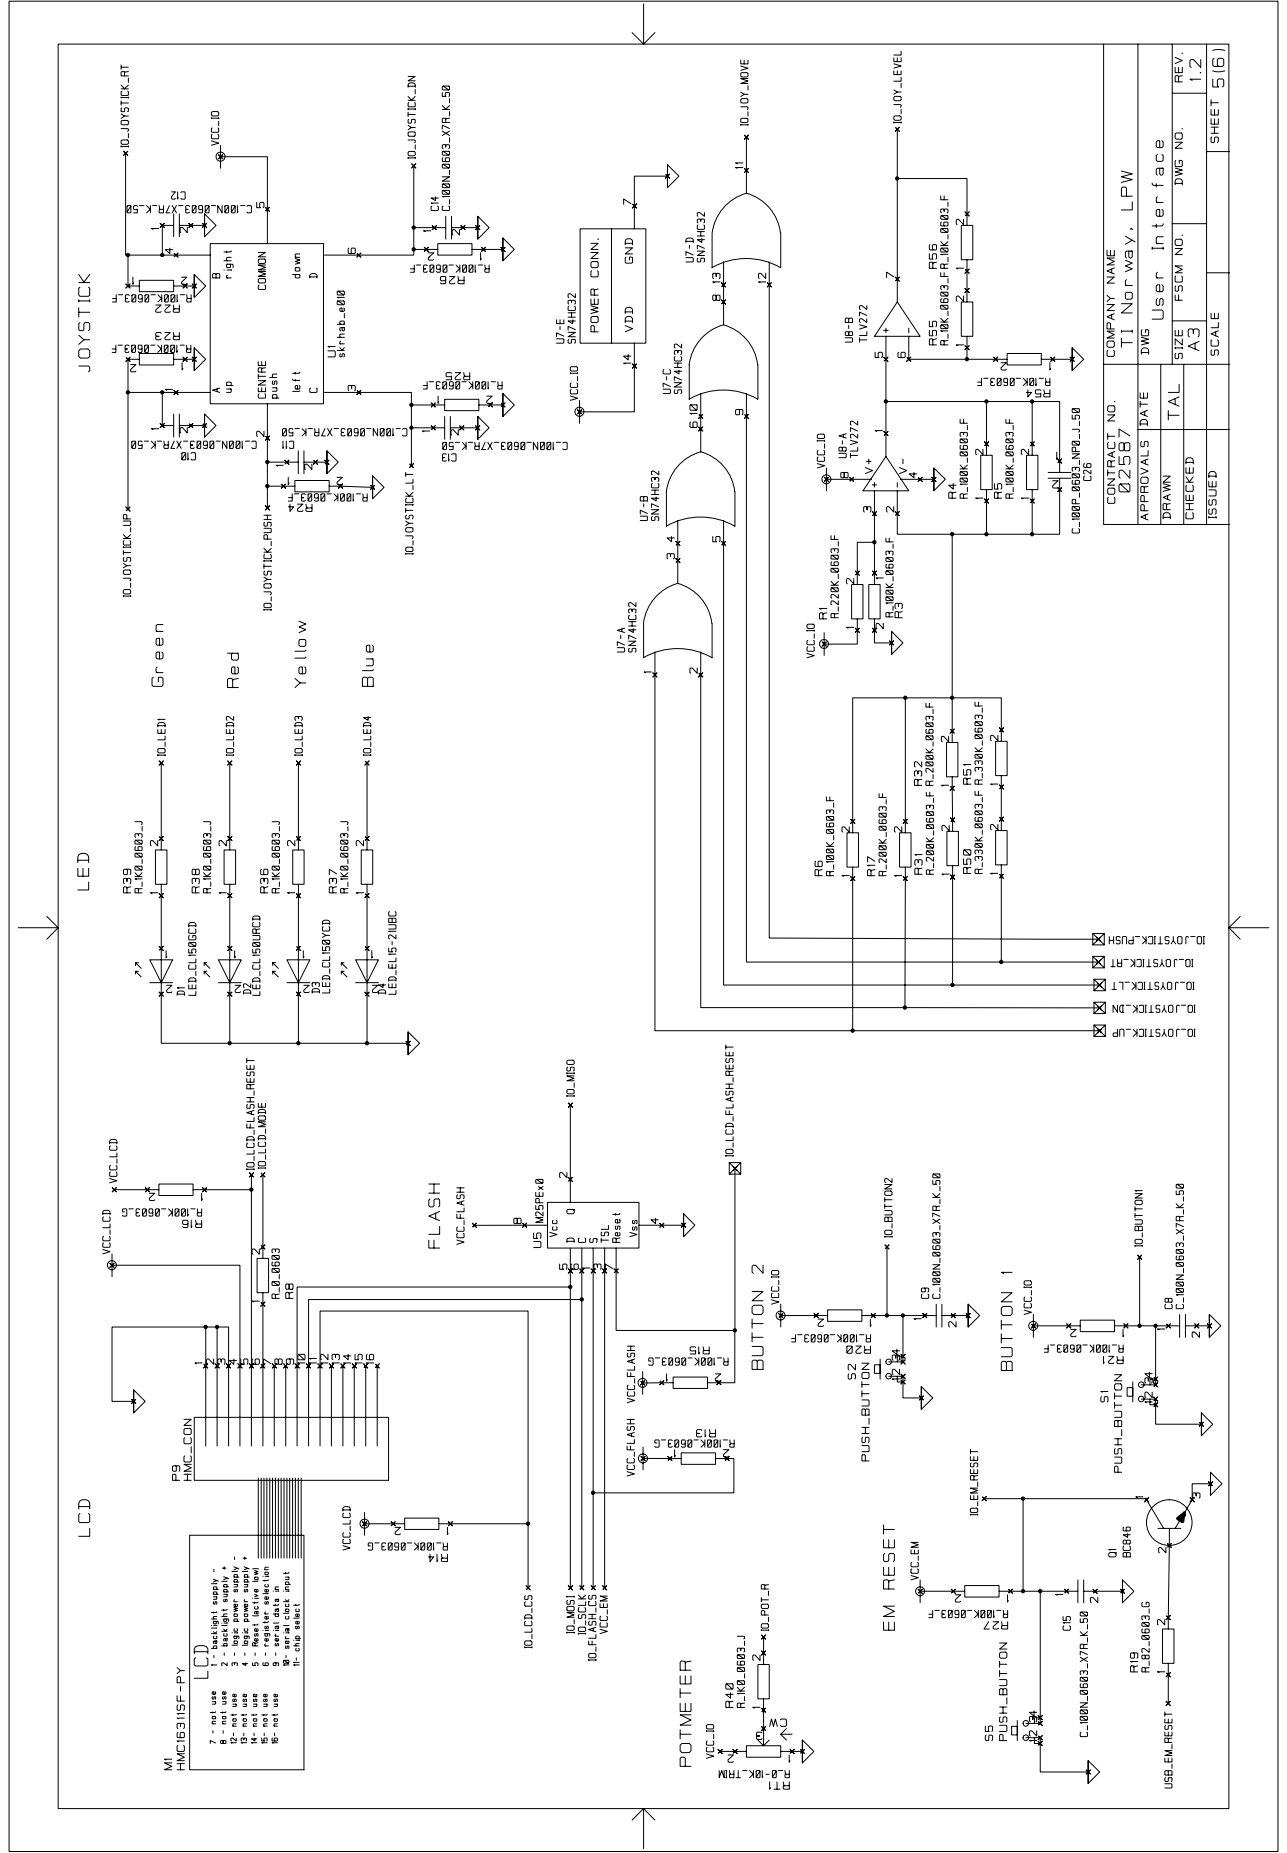
[picture p45: page 5]

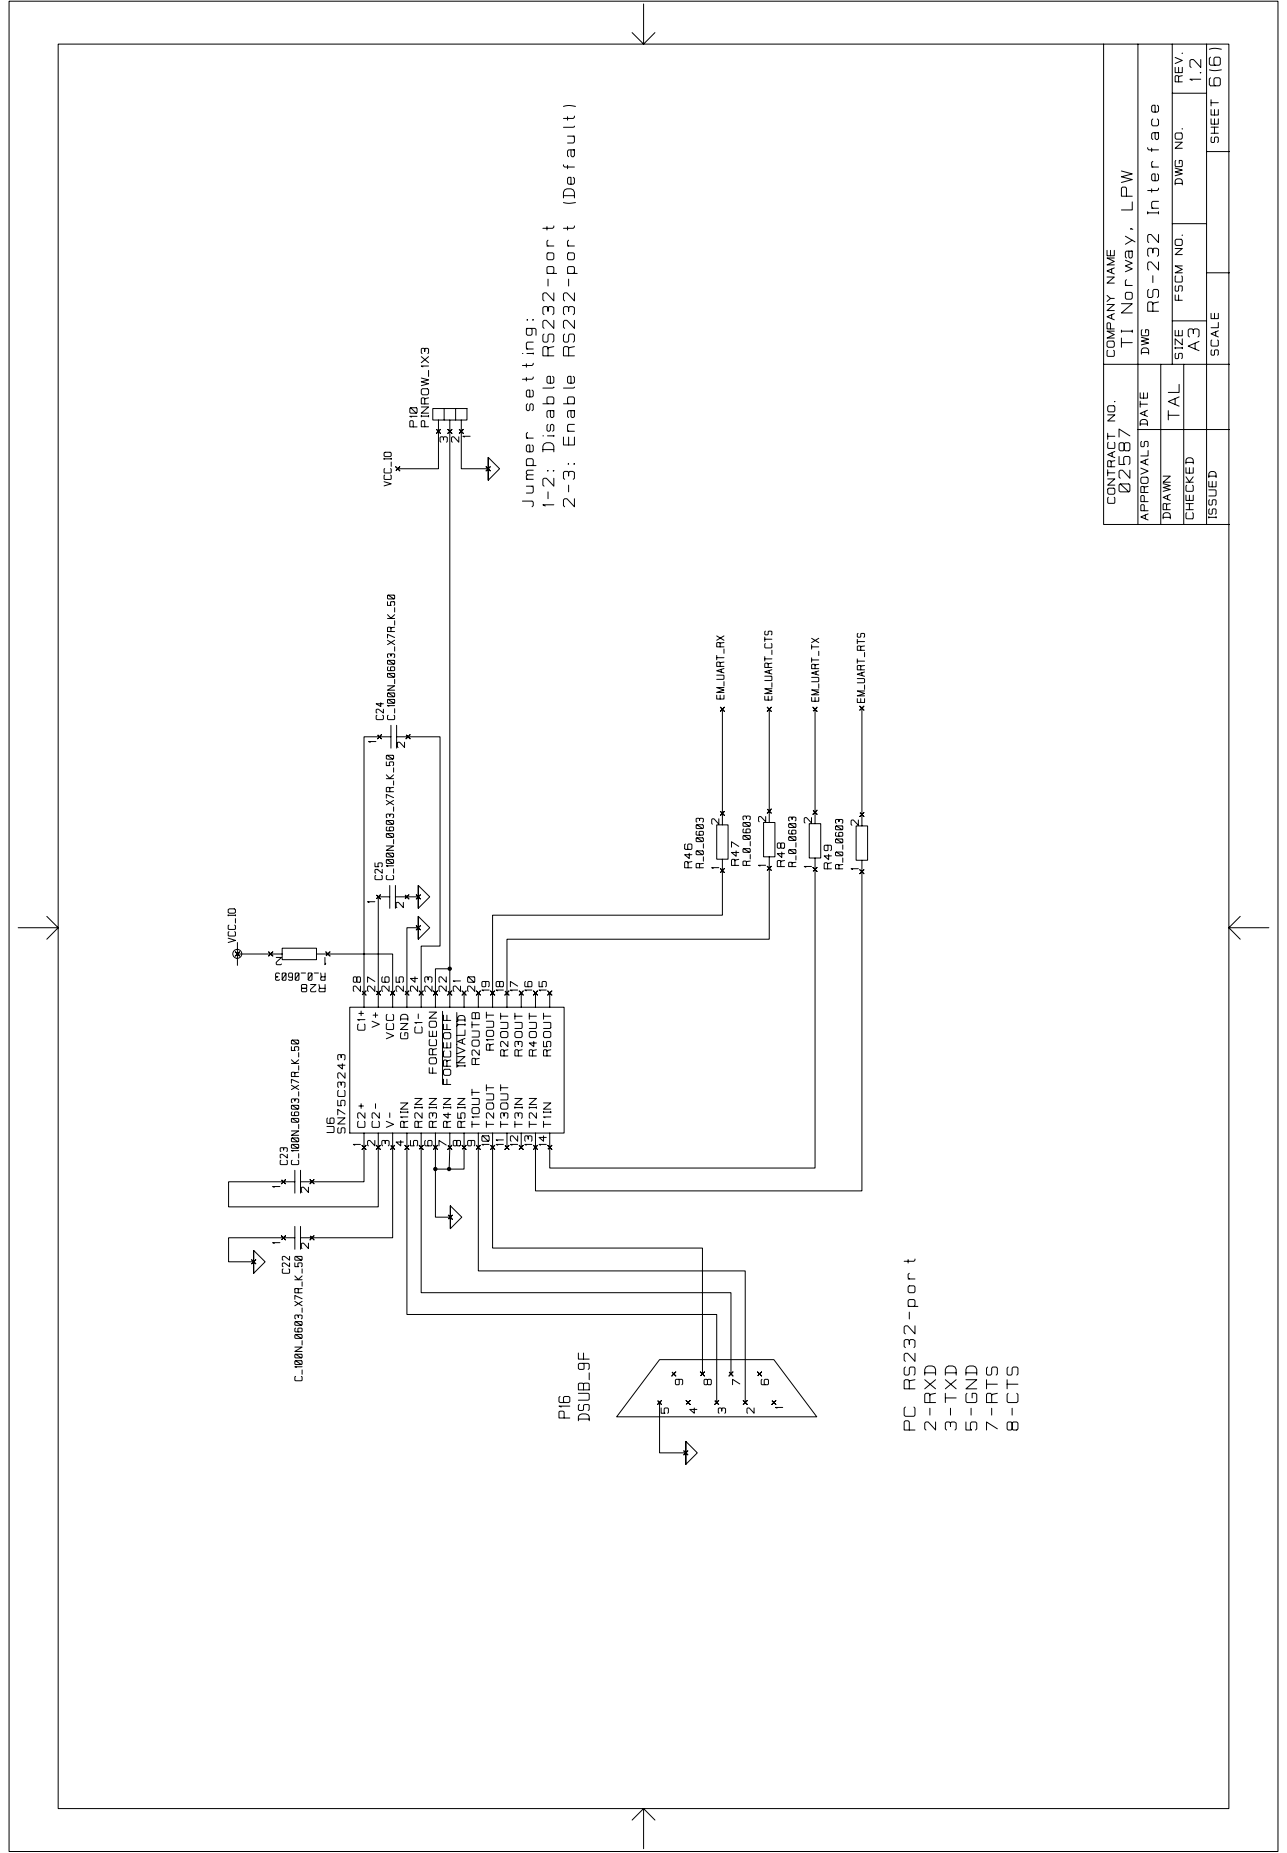
[picture p46: page 6]
