blueintegral/Level/firmware/levelfirmware/msp430-gcc/RfRegSettings.c

#include "RF1A.h"

//RF_SETTINGS rfSettings = {
//    0x06,   // FSCTRL1   Frequency synthesizer control.
//    0x00,   // FSCTRL0   Frequency synthesizer control.
//    0x21,   // FREQ2     Frequency control word, high byte.
//    0x62,   // FREQ1     Frequency control word, middle byte.
//    0x76,   // FREQ0     Frequency control word, low byte.
//    0x2B,   // MDMCFG4   Modem configuration.
//    0x3B,   // MDMCFG3   Modem configuration.
//    0x75,   // MDMCFG2   Modem configuration.
//    0x22,   // MDMCFG1   Modem configuration.
//    0xF8,   // MDMCFG0   Modem configuration.
//    0x00,   // CHANNR    Channel number.
//    0x15,   // DEVIATN   Modem deviation setting (when FSK modulation is enabled).
//    0x56,   // FREND1    Front end RX configuration.
//    0x10,   // FREND0    Front end TX configuration.
//    0x18,   // MCSM0     Main Radio Control State Machine configuration.
//    0x16,   // FOCCFG    Frequency Offset Compensation Configuration.
//    0x6C,   // BSCFG     Bit synchronization Configuration.
//    0x03,   // AGCCTRL2  AGC control.
//    0x40,   // AGCCTRL1  AGC control.
//    0x91,   // AGCCTRL0  AGC control.
//    0xEA,   // FSCAL3    Frequency synthesizer calibration.
//    0x2A,   // FSCAL2    Frequency synthesizer calibration.
//    0x00,   // FSCAL1    Frequency synthesizer calibration.
//    0x1F,   // FSCAL0    Frequency synthesizer calibration.
//    0x59,   // FSTEST    Frequency synthesizer calibration.
//    0x81,   // TEST2     Various test settings.
//    0x31,   // TEST1     Various test settings.
//    0x09,   // TEST0     Various test settings.
//    0x47,   // FIFOTHR   RXFIFO and TXFIFO thresholds.
//    0x29,   // IOCFG2    GDO2 output pin configuration.
//    0x06,   // IOCFG0    GDO0 output pin configuration. Refer to SmartRF® Studio User Manual for detailed pseudo register explanation.
//    0x04,   // PKTCTRL1  Packet automation control.
//   0x05,   // PKTCTRL0  Packet automation control.
//    0x00,   // ADDR      Device address.
//    0xFF    // PKTLEN    Packet length.
//};
