blueintegral/Level/firmware/levelfirmware/msp430-gcc/Include/HAL.h

/*
 * HAL.h
 *
 *  Created on: Sep 21, 2014
 *      Author: hunter
 */

#ifndef HAL_H_
#define HAL_H_
//Function prototypes
int set_datarate(float rate);
int set_frequency(int freq);
int set_power(int power);
int set_mode(char * mode);
//int get_status(void);
//int get_device_id(void);
//int set_message(char *buf, int length);
//int transmit_now(void);
//int get_message(void);
//int set_modulation(char *mod);




#endif /* HAL_H_ */
