blueintegral/Level/firmware/example code/CC430x513x RF examples/RF_Examples_CCS/Asynchronous_Communication/HAL/RfRegSettings_RX.c

#include "RF1A.h"

#ifdef MHZ_915

// Chipcon
// Product = CC430Fx13x
// Chip version = A   (HW Rev. 0x10)
// Crystal accuracy = 10 ppm
// X-tal frequency = 26 MHz
// RF output power = 0 dBm
// RX filterbandwidth = 101.562500 kHz
// Deviation = 19 kHz
// Datarate = 38.383484 kBaud
// Modulation = (1) GFSK
// Manchester enable = (0) Manchester disabled
// RF Frequency = 914.999969 MHz
// Channel spacing = 199.951172 kHz
// Channel number = 0
// Optimization = -
// Sync mode = (0) No preamble/sync
// Format of RX/TX data = (3) Asynchronous transparent mode. Data in on GDO0 and Data out on either of the GDO pins
// CRC operation = (0) CRC disabled for TX and RX
// Forward Error Correction = (0) FEC disabled
// Length configuration = (2) Enable infinite length packets.
// Packetlength = 255
// Preamble count = (2)  4 bytes
// Append status = 1
// Address check = (0) No address check
// FIFO autoflush = 0
// Device address = 0
// GDO0 signal selection = (13) Serial transparent Data Output
// GDO2 signal selection = (13) Serial transparent Data Output
RF_SETTINGS rfSettings = {
    0x08,   // FSCTRL1   Frequency synthesizer control.
    0x00,   // FSCTRL0   Frequency synthesizer control.
    0x23,   // FREQ2     Frequency control word, high byte.
    0x31,   // FREQ1     Frequency control word, middle byte.
    0x3B,   // FREQ0     Frequency control word, low byte.
    0xCA,   // MDMCFG4   Modem configuration.
    0x83,   // MDMCFG3   Modem configuration.
    0x90,   // MDMCFG2   Modem configuration.
    0x22,   // MDMCFG1   Modem configuration.
    0xF8,   // MDMCFG0   Modem configuration.
    0x00,   // CHANNR    Channel number.
    0x34,   // DEVIATN   Modem deviation setting (when FSK modulation is enabled).
    0x56,   // FREND1    Front end RX configuration.
    0x10,   // FREND0    Front end TX configuration.
    0x18,   // MCSM0     Main Radio Control State Machine configuration.
    0x16,   // FOCCFG    Frequency Offset Compensation Configuration.
    0x6C,   // BSCFG     Bit synchronization Configuration.
    0x43,   // AGCCTRL2  AGC control.
    0x40,   // AGCCTRL1  AGC control.
    0x91,   // AGCCTRL0  AGC control.
    0xE9,   // FSCAL3    Frequency synthesizer calibration.
    0x2A,   // FSCAL2    Frequency synthesizer calibration.
    0x00,   // FSCAL1    Frequency synthesizer calibration.
    0x1F,   // FSCAL0    Frequency synthesizer calibration.
    0x59,   // FSTEST    Frequency synthesizer calibration.
    0x81,   // TEST2     Various test settings.
    0x35,   // TEST1     Various test settings.
    0x09,   // TEST0     Various test settings.
    0x47,   // FIFOTHR   RXFIFO and TXFIFO thresholds.
    0x0D,   // IOCFG2    GDO2 output pin configuration.
    0x0D,   // IOCFG0D   GDO0 output pin configuration. Refer to SmartRF® Studio User Manual for detailed pseudo register explanation.
    0x04,   // PKTCTRL1  Packet automation control.
    0x32,   // PKTCTRL0  Packet automation control.
    0x00,   // ADDR      Device address.
    0xFF    // PKTLEN    Packet length.
};

#elif defined MHZ_868

// Chipcon
// Product = CC430Fx13x
// Chip version = A   (HW Rev. 0x10)
// Crystal accuracy = 10 ppm
// X-tal frequency = 26 MHz
// RF output power = 0 dBm
// RX filterbandwidth = 101.562500 kHz
// Deviation = 19 kHz
// Datarate = 38.383484 kBaud
// Modulation = (1) GFSK
// Manchester enable = (0) Manchester disabled
// RF Frequency = 867.999939 MHz
// Channel spacing = 199.951172 kHz
// Channel number = 0
// Optimization = -
// Sync mode = (0) No preamble/sync
// Format of RX/TX data = (3) Asynchronous transparent mode. Data in on GDO0 and Data out on either of the GDO pins
// CRC operation = (0) CRC disabled for TX and RX
// Forward Error Correction = (0) FEC disabled
// Length configuration = (2) Enable infinite length packets.
// Packetlength = 255
// Preamble count = (2)  4 bytes
// Append status = 1
// Address check = (0) No address check
// FIFO autoflush = 0
// Device address = 0
// GDO0 signal selection = (13) Serial transparent Data Output
// GDO2 signal selection = (13) Serial transparent Data Output
RF_SETTINGS rfSettings = {
    0x08,   // FSCTRL1   Frequency synthesizer control.
    0x00,   // FSCTRL0   Frequency synthesizer control.
    0x21,   // FREQ2     Frequency control word, high byte.
    0x62,   // FREQ1     Frequency control word, middle byte.
    0x76,   // FREQ0     Frequency control word, low byte.
    0xCA,   // MDMCFG4   Modem configuration.
    0x83,   // MDMCFG3   Modem configuration.
    0x90,   // MDMCFG2   Modem configuration.
    0x22,   // MDMCFG1   Modem configuration.
    0xF8,   // MDMCFG0   Modem configuration.
    0x00,   // CHANNR    Channel number.
    0x34,   // DEVIATN   Modem deviation setting (when FSK modulation is enabled).
    0x56,   // FREND1    Front end RX configuration.
    0x10,   // FREND0    Front end TX configuration.
    0x18,   // MCSM0     Main Radio Control State Machine configuration.
    0x16,   // FOCCFG    Frequency Offset Compensation Configuration.
    0x6C,   // BSCFG     Bit synchronization Configuration.
    0x43,   // AGCCTRL2  AGC control.
    0x40,   // AGCCTRL1  AGC control.
    0x91,   // AGCCTRL0  AGC control.
    0xE9,   // FSCAL3    Frequency synthesizer calibration.
    0x2A,   // FSCAL2    Frequency synthesizer calibration.
    0x00,   // FSCAL1    Frequency synthesizer calibration.
    0x1F,   // FSCAL0    Frequency synthesizer calibration.
    0x59,   // FSTEST    Frequency synthesizer calibration.
    0x81,   // TEST2     Various test settings.
    0x35,   // TEST1     Various test settings.
    0x09,   // TEST0     Various test settings.
    0x47,   // FIFOTHR   RXFIFO and TXFIFO thresholds.
    0x0D,   // IOCFG2    GDO2 output pin configuration.
    0x0D,   // IOCFG0D   GDO0 output pin configuration. Refer to SmartRF® Studio User Manual for detailed pseudo register explanation.
    0x04,   // PKTCTRL1  Packet automation control.
    0x32,   // PKTCTRL0  Packet automation control.
    0x00,   // ADDR      Device address.
    0xFF    // PKTLEN    Packet length.
};

#endif

#if !defined (MHZ_868) && !defined (MHZ_915)
#error "Please select MHZ_868 or MHZ_915 as the active project configuration" 
#endif
